BoujeeEnjinia1701/thermabrick/cad/drawings/TBK-DWG-001.pdf

CONCEPT, NOT FOR FABRICATION | ThermaBrick · github.com/BoujeeEnjinia1701/thermabrick

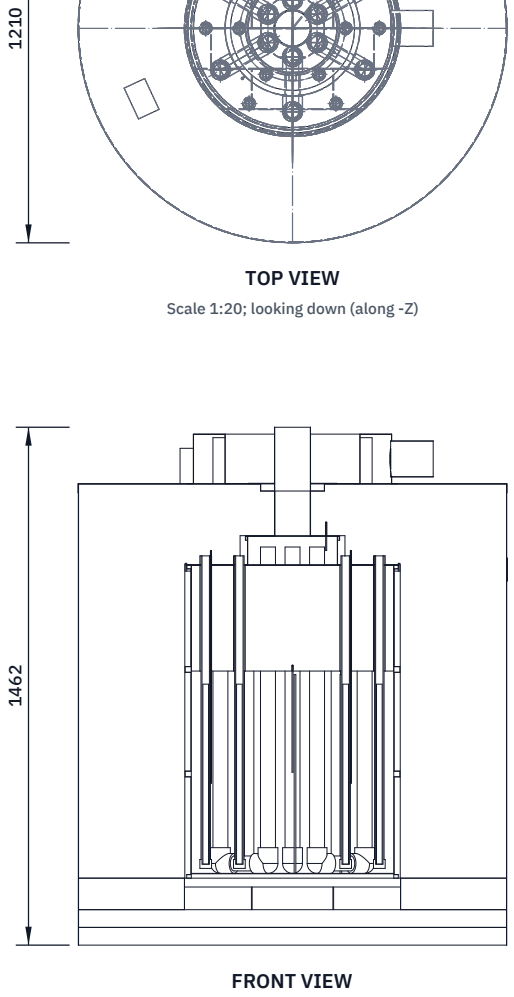
[picture p46: figure]
FRONT VIEW; TOP VIEW; Scale 1:20; looking down (along -Z)

Scale 1:20; looking at the front (along +Y)

RIGHT VIEW
Scale 1:20; looking at the right side (along -X)

1212

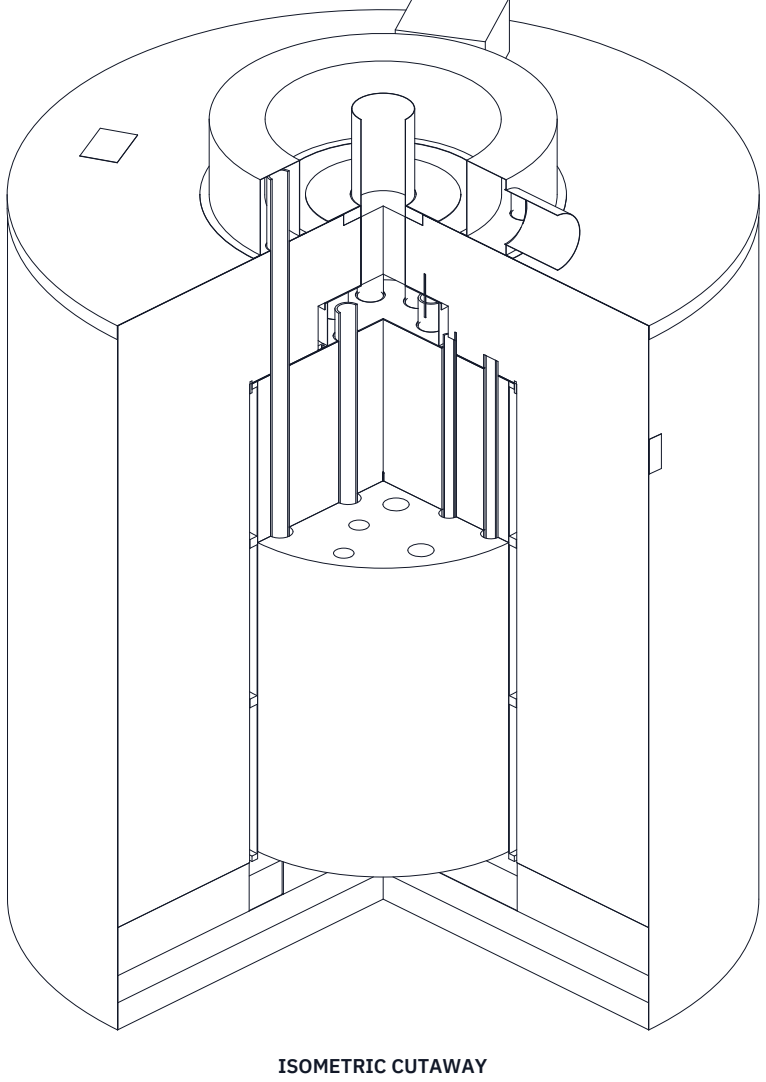
[picture p47: figure]
ISOMETRIC CUTAWAY

Quarter removed, not to scale; seen from the front right and above, about 30 deg elevation

KEY DATA AND NOTES
STORAGE | 210 kg dry silica sand, 18.3 kWh(th) between 150 and 450 °C mean
CHARGE | 12 cartridge heaters, 250 W each, 3.0 kW at 240 V; sand and well wall 550 °C max
DISCHARGE | Six 1-1/4 in U-tubes, 1.0 kW rated, 1.5 kW boost; supply air 50 °C via mixing tee
ENVELOPE | 1,209 mm dia x 1,462 mm high; about 415 kg; slab floor only
SECTION A-A | Front view is cut on the XZ plane through four heater wells; sand omitted for clarity
SAND LEVEL | 571 mm above drum floor; headspace filled with 298 mm AES blanket and stone wool
LABELS | HOT SURFACES INSIDE on the jacket, HOT OUTLET on the cap, DANGER 240 V on the junction box (96 x 64 and 90 x 44 mm)
REFERENCE | TBK-PRC-001 design precis, TBK-CAL-001 sizing, TBK-BLD-001 build plan, bom/bom.csv
REV | DESCRIPTION | DATE | BY
P1 | First issue: general arrangement of the v0.2 design | 2026-09-24 | AC
P2 | Made constructable: base, fittings, plenum, cap, box (TBK-DDR-003) | 2026-09-30 | AC
P3 | Warning labels added: jacket, cap, junction box (BOM line 47, TBK-DEC-001) | 2026-10-02 | AC
THERMABRICK | github.com/BoujeeEnjinia1701/thermabrick

# General arrangement

DRAWING NO.
TBK-DWG-001

REV
P3

SHEET
1 of 1

SIZE

## ANSI B

SCALE
1:20

UNITS
mm
PROJECTION | DATE
2026-10-02

DRAWN

### Amish Chadha

MATERIAL / NOTES
Carbon steel drum and pipe; AES blanket and stone wool; galvanized jacket. See bom/bom.csv
Licensed CERN-OHL-S-2.0 · Design Molecule Lab · designmolecule.com | Generated from cad/src; do not edit by hand
