BoujeeEnjinia1701/thermabrick/cad/drawings/TBK-DWG-101.pdf

BUILD PLAN SKETCH, PLAN NOT YET BUILT ThermaBrick · github.com/BoujeeEnjinia1701/thermabrick

FRONT VIEW
Scale 1:20; looking at the front (along +Y)

TOP VIEW
Scale 1:20; looking down (along -Z)

RIGHT VIEW
Scale 1:20; looking at the right side (along -X)

1208

1208 189

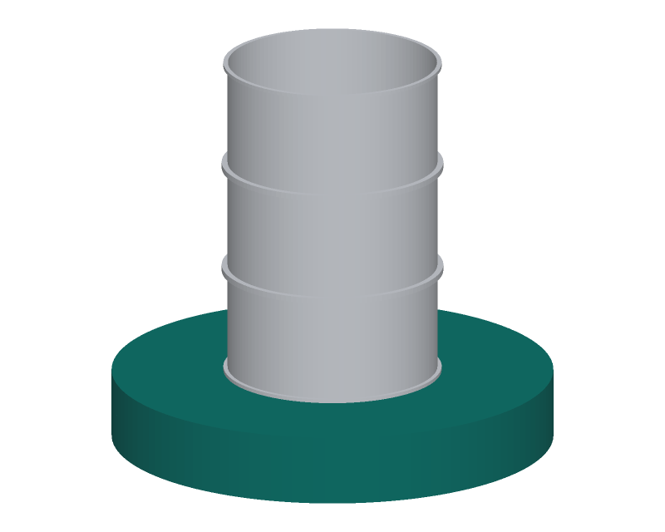
[picture p48: figure]

WHERE IT GOES
This part in colour, its neighbours in grey

HOW TO MAKE IT AND HOW IT FITS
Four layers, 189 mm in all, 1,208 mm across (the inside of the jacket).
Boards: two layers of 50 mm stone wool board, each from two 610 x 1,219 mm boards butted into a 1,219 mm square and cut to a 1,208 mm disc.
Turn the top layer 90 degrees so the joints cross.
Firebrick: one course laid flat (64 mm), 610 mm disc in the middle,
bricks in staggered rows, cut with a saw to the circle (layout picture).
AES board: one 25 mm board cut to a 610 mm disc, laid on the bricks. Ring: 89 mm stone wool batt cut into segments to fill from the 610 mm disc out to 1,208 mm, level with the top of the AES board.
Fit: the drum's bottom rim (597 mm) stands on the AES disc, 6 mm in from its edge, over the firebrick, which carries the load.
Check: the top is flat within 3 mm across a straight edge.
REV | DESCRIPTION | DATE | BY
P1 | Making sketch for the prototype build plan | 2026-09-30 | AC
THERMABRICK | github.com/BoujeeEnjinia1701/thermabrick

## ThermaBrick base: making sketch

DRAWING NO.
TBK-DWG-101

REV
P1

SHEET
1 of 1

SIZE

## ANSI B

SCALE
1:20

UNITS
mm
PROJECTION | DATE
2026-09-30

DRAWN
Amish Chadha

MATERIAL / NOTES
Stone wool board 50 mm; K-23 firebrick; AES board 25 mm; stone wool batt 89 mm
Licensed CERN-OHL-S-2.0 · Design Molecule Lab · designmolecule.com | Generated from cad/src; do not edit by hand
