BoujeeEnjinia1701/thermabrick/cad/drawings/TBK-DWG-102.pdf

BUILD PLAN SKETCH, PLAN NOT YET BUILT ThermaBrick · github.com/BoujeeEnjinia1701/thermabrick

FRONT VIEW
Scale 1:10; looking at the front (along +Y)

TOP VIEW
Scale 1:10; looking down (along -Z)

RIGHT VIEW
Scale 1:10; looking at the right side (along -X)

606

606 22

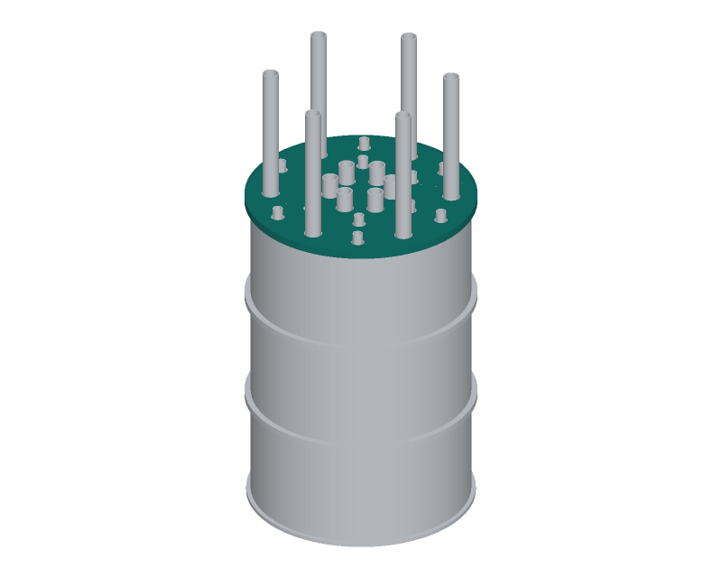
[picture p49: figure]

WHERE IT GOES
This part in colour, its neighbours in grey

HOW TO MAKE IT AND HOW IT FITS
Drill the lid with the template (TBK-DWG-103) clamped on it as a guide. Twelve 36 mm holes for the heater wells: six on a 150 mm radius at
0, 60, 120 ... degrees and six on a 245 mm radius at the same angles. Twelve 48 mm holes for the U-tube legs: six on 80 mm and six on 235 mm radius at 30, 90, 150 ... degrees (between the wells).
Four 6 mm holes for the sand thermocouples (lid layout picture).
Cut with bi-metal hole saws at low speed with cutting oil; deburr.
Mark a line at 0 degrees on the lid and the drum rim to line them up. Fit: the lid drops over all 24 pipe ends, the well holes leaving a
4.6 mm gap (a T1 to T3 sheath fits beside its well) and the leg holes 2.9 mm. An AES rope collar is laid round every pipe on the lid. Check: lay the template on the lid; every hole lines up.
REV | DESCRIPTION | DATE | BY
P1 | Making sketch for the prototype build plan | 2026-09-30 | AC
THERMABRICK | github.com/BoujeeEnjinia1701/thermabrick

## ThermaBrick drum lid: drilling sketch

DRAWING NO.
TBK-DWG-102

REV
P1

SHEET
1 of 1

SIZE

## ANSI B

SCALE
1:10

UNITS
mm
PROJECTION | DATE
2026-09-30

DRAWN
Amish Chadha

MATERIAL / NOTES
The drum's own 16 ga steel lid and bolted closing ring
Licensed CERN-OHL-S-2.0 · Design Molecule Lab · designmolecule.com | Generated from cad/src; do not edit by hand
