BoujeeEnjinia1701/thermabrick/cad/drawings/TBK-DWG-103.pdf

BUILD PLAN SKETCH, PLAN NOT YET BUILT ThermaBrick · github.com/BoujeeEnjinia1701/thermabrick

FRONT VIEW
Scale 1:10; looking at the front (along +Y)

TOP VIEW
Scale 1:10; looking down (along -Z)

RIGHT VIEW
Scale 1:10; looking at the right side (along -X)

597

597 18

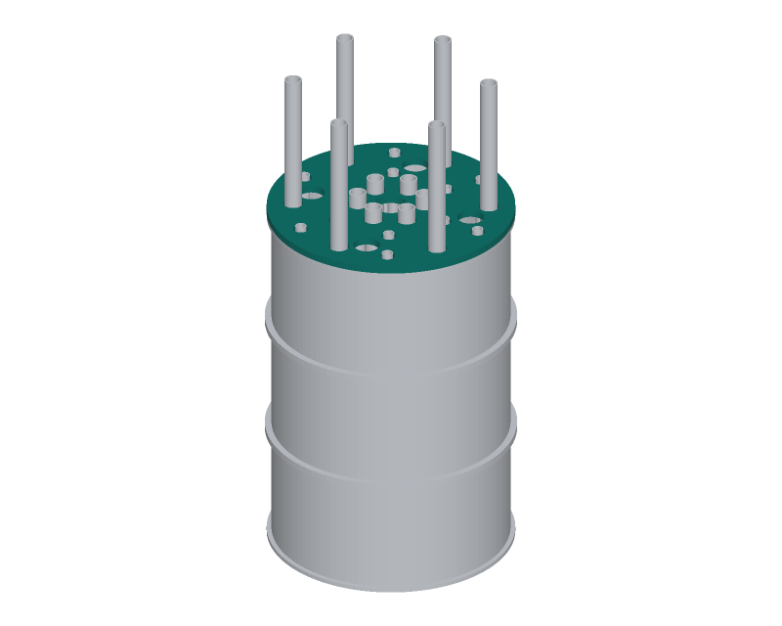
[picture p50: figure]

WHERE IT GOES
This part in colour, its neighbours in grey

HOW TO MAKE IT AND HOW IT FITS
A temporary jig. Cut a 597 mm disc from 18 mm plywood: it sits on the drum's top rim, where the lid will go.
Drill the same holes as the lid (36 mm wells, 48 mm legs, 6 mm sheaths) from the lid layout picture, with the 0 degree line marked.
Pour holes: one 80 mm hole in the centre and four 64 mm holes on a 200 mm radius at 15, 105, 195 and 285 degrees.
Drill the template first and use it to drill the lid, so both match.
Fit: the template drops over the pipe ends and holds every well, U-tube leg and sheath upright while sand is poured through the pour holes. Lift it off before the headspace insulation goes in.
Check: it lies flat on the rim with all 24 pipes through it.
REV | DESCRIPTION | DATE | BY
P1 | Making sketch for the prototype build plan | 2026-09-30 | AC
THERMABRICK | github.com/BoujeeEnjinia1701/thermabrick

## ThermaBrick setting template: making sketch

DRAWING NO.
TBK-DWG-103

REV
P1

SHEET
1 of 1

SIZE

## ANSI B

SCALE
1:10

UNITS
mm
PROJECTION | DATE
2026-09-30

DRAWN
Amish Chadha

MATERIAL / NOTES
Exterior plywood 18 mm
Licensed CERN-OHL-S-2.0 · Design Molecule Lab · designmolecule.com | Generated from cad/src; do not edit by hand
