BoujeeEnjinia1701/thermabrick/cad/drawings/TBK-DWG-104.pdf

BUILD PLAN SKETCH, PLAN NOT YET BUILT ThermaBrick · github.com/BoujeeEnjinia1701/thermabrick

FRONT VIEW
Scale 1:10; looking at the front (along +Y)

TOP VIEW
Scale 1:10; looking down (along -Z)

RIGHT VIEW
Scale 1:10; looking at the right side (along -X)

33

33 882

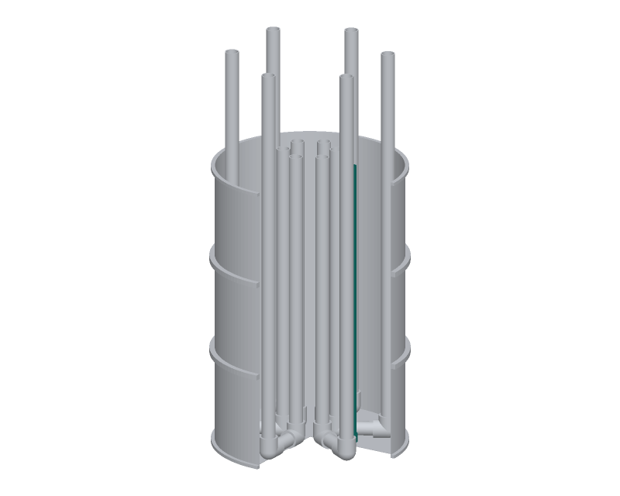
[picture p51: figure]

WHERE IT GOES
This part in colour, its neighbours in grey

HOW TO MAKE IT AND HOW IT FITS
Cut twelve lengths of 876 mm from four 10 ft pipes (three per pipe). Thread one end 3/4 in NPT (rented pipe threader); ream and deburr. Clean off cutting oil with degreaser: oil smokes on first heat.
Coat the thread with nickel anti-seize (no PTFE tape or paste) and screw on the cap hand tight plus one and a half turns.
The open top end is square cut and deburred so a heater slides in. Fit: the cap stands on a levelled 14 mm first lift of sand; the template and then the lid hold the top, which ends 25 mm above the lid.
Each 508 mm heater rests on the cap inside, its heated part 26 to 483 mm above the drum floor; its leads rise out of the open top. Check: length 876 mm plus cap, within 3 mm; a 16 mm rod slides to the bottom freely.
REV | DESCRIPTION | DATE | BY
P1 | Making sketch for the prototype build plan | 2026-09-30 | AC
THERMABRICK | github.com/BoujeeEnjinia1701/thermabrick

## ThermaBrick heater well (make 12): making sketch

DRAWING NO.
TBK-DWG-104

REV
P1

SHEET
1 of 1

SIZE

## ANSI B

SCALE
1:10

UNITS
mm
PROJECTION | DATE
2026-09-30

DRAWN
Amish Chadha

MATERIAL / NOTES
Black steel pipe 3/4 in Sch 40 (26.7 mm), malleable iron cap 3/4 in NPT
Licensed CERN-OHL-S-2.0 · Design Molecule Lab · designmolecule.com | Generated from cad/src; do not edit by hand
