BoujeeEnjinia1701/thermabrick/cad/drawings/TBK-DWG-105.pdf

BUILD PLAN SKETCH, PLAN NOT YET BUILT ThermaBrick · github.com/BoujeeEnjinia1701/thermabrick

FRONT VIEW
Scale 1:10; looking at the front (along +Y)

TOP VIEW
Scale 1:10; looking down (along -Z)

RIGHT VIEW
Scale 1:10; looking at the right side (along -X)

211

56 1230

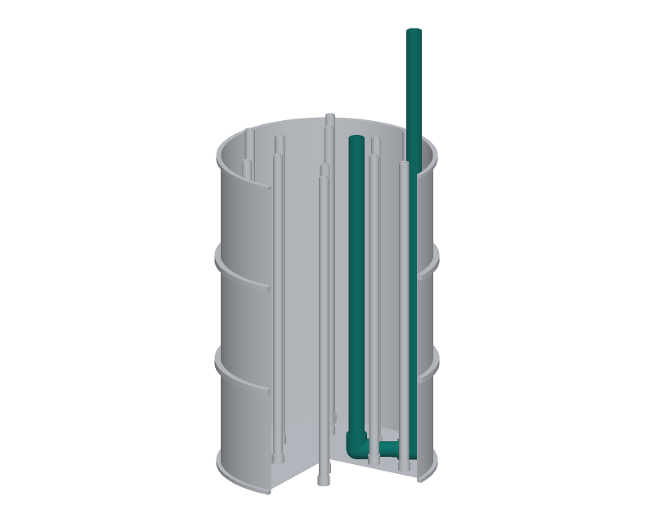
[picture p52: figure]

WHERE IT GOES
This part in colour, its neighbours in grey

HOW TO MAKE IT AND HOW IT FITS
Cut six inlet legs 1175 mm long (two per 10 ft pipe) and six outlet legs 866 mm (three per pipe). Thread one end of each. Degrease, coat every thread with nickel anti-seize, then join: outlet leg, elbow, 4 in nipple, elbow, inlet leg, wrench tight. Turn the second elbow so both legs stand parallel, in one plane. Leg centres 155 mm apart (the fittings make 155.6 mm).
The elbows rest on the drum floor; the run is 28 mm above it.
Fit: the short leg (outlet) stands on the 80 mm circle and ends inside the collector; the long leg (inlet) on the 235 mm circle, ending inside the inlet plenum, 130 mm above the jacket cap.
Check: legs parallel within 3 mm over their length; blow through
it to clear swarf.
REV | DESCRIPTION | DATE | BY
P1 | Making sketch for the prototype build plan | 2026-09-30 | AC
THERMABRICK | github.com/BoujeeEnjinia1701/thermabrick

## ThermaBrick U-tube (make 6): making sketch

DRAWING NO.
TBK-DWG-105

REV
P1

SHEET
1 of 1

SIZE

## ANSI B

SCALE
1:10

UNITS
mm
PROJECTION | DATE
2026-09-30

DRAWN
Amish Chadha

MATERIAL / NOTES
Black steel pipe 1-1/4 in Sch 40; two 90 degree elbows; 1-1/4 x 4 in nipple
Licensed CERN-OHL-S-2.0 · Design Molecule Lab · designmolecule.com | Generated from cad/src; do not edit by hand
