BoujeeEnjinia1701/thermabrick/cad/drawings/TBK-DWG-106.pdf

BUILD PLAN SKETCH, PLAN NOT YET BUILT ThermaBrick · github.com/BoujeeEnjinia1701/thermabrick

FRONT VIEW
Scale 1:10; looking at the front (along +Y)

TOP VIEW
Scale 1:10; looking down (along -Z)

RIGHT VIEW
Scale 1:10; looking at the right side (along -X)

266

293 388

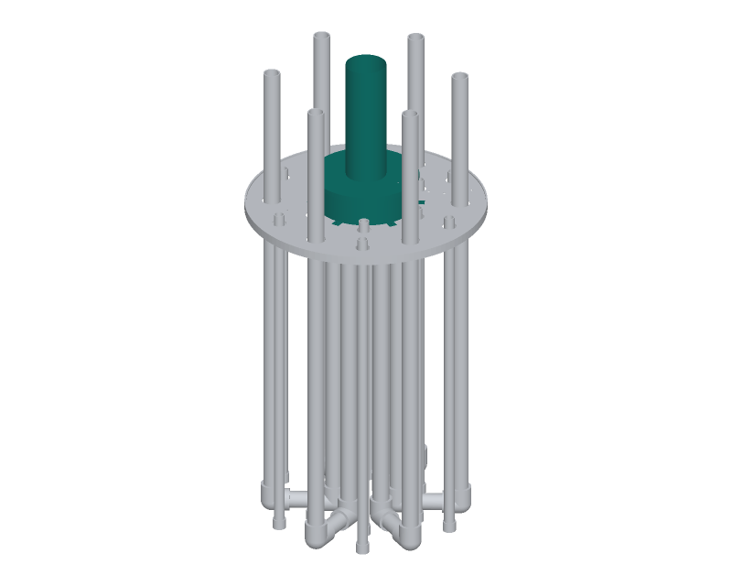
[picture p53: figure]

WHERE IT GOES
This part in colour, its neighbours in grey

HOW TO MAKE IT AND HOW IT FITS
Ring: cut an 80 mm band from 10 in (254 mm) black stovepipe. Tabs: at the foot, at 30, 90, 150 ... degrees, cut six slits 20 mm deep and 20 mm apart and fold the tabs out flat. Drill each for a 4.8 mm steel rivet, 10 mm from the ring.
Top: cut a 266 mm disc from 18 ga uncoated steel, fold a 12 mm edge down over the ring and rivet it in six places.
Cut a 4 in hole in the middle and rivet in the 4 in crimped start collar; fit the 4 in pipe to 160 mm above the jacket cap.
Drill a 4 mm hole 95 mm from the centre for thermocouple T8.
Fit: tabs riveted to the lid between the inner wells; AES rope pressed round the foot of the ring. The six short legs end inside it.
No zinc: use uncoated steel and steel rivets only.
REV | DESCRIPTION | DATE | BY
P1 | Making sketch for the prototype build plan | 2026-09-30 | AC
THERMABRICK | github.com/BoujeeEnjinia1701/thermabrick

## ThermaBrick collector and outlet: making sketch

DRAWING NO.
TBK-DWG-106

REV
P1

SHEET
1 of 1

SIZE

## ANSI B

SCALE
1:10

UNITS
mm
PROJECTION | DATE
2026-09-30

DRAWN
Amish Chadha

MATERIAL / NOTES
10 in black stovepipe 24 ga; 18 ga steel sheet; 4 in start collar and pipe
Licensed CERN-OHL-S-2.0 · Design Molecule Lab · designmolecule.com | Generated from cad/src; do not edit by hand
