BoujeeEnjinia1701/thermabrick/cad/drawings/TBK-DWG-107.pdf

BUILD PLAN SKETCH, PLAN NOT YET BUILT ThermaBrick · github.com/BoujeeEnjinia1701/thermabrick

FRONT VIEW
Scale 1:20; looking at the front (along +Y)

TOP VIEW
Scale 1:20; looking down (along -Z)

RIGHT VIEW
Scale 1:20; looking at the right side (along -X)

1209

1209 1302

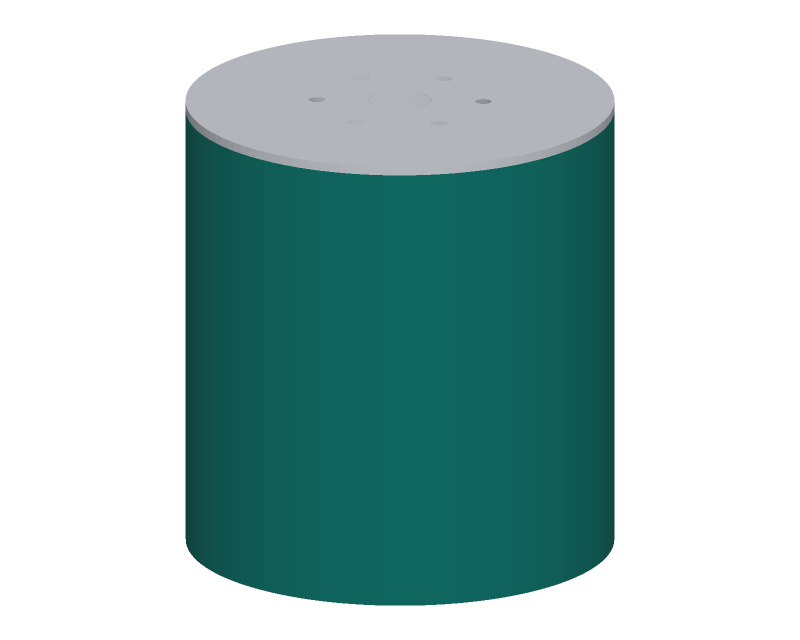
[picture p54: figure]

WHERE IT GOES
This part in colour, its neighbours in grey

HOW TO MAKE IT AND HOW IT FITS
Three rows of 610 mm flashing, each 3,850 mm long (3,800 mm round plus a 50 mm lap), wrapped round the side insulation.
Bottom row on the floor; the second laps 25 mm outside it; the top row is cut to width so the side ends 1,302 mm above the floor.
Pull each row tight with ratchet straps over the insulation, then rivet the vertical lap every 100 mm with 4.8 mm aluminium rivets. Rivet the row laps every 150 mm. Stagger the vertical laps.
Inside diameter 1,208 mm: the insulation is 317 mm thick all round. Fit: the cap's 25 mm skirt sits outside the top row and is held by sheet metal screws (not rivets) so the cap can come off.
The jacket runs at about 26 degrees C, so galvanized steel is fine. Check: round within 10 mm on two diameters; no gaps at the laps.
REV | DESCRIPTION | DATE | BY
P1 | Making sketch for the prototype build plan | 2026-09-30 | AC
THERMABRICK | github.com/BoujeeEnjinia1701/thermabrick

## ThermaBrick jacket side: making sketch

DRAWING NO.
TBK-DWG-107

REV
P1

SHEET
1 of 1

SIZE

## ANSI B

SCALE
1:20

UNITS
mm
PROJECTION | DATE
2026-09-30

DRAWN
Amish Chadha

MATERIAL / NOTES
Galvanized steel flashing 0.6 mm, 610 mm wide coil
Licensed CERN-OHL-S-2.0 · Design Molecule Lab · designmolecule.com | Generated from cad/src; do not edit by hand
