BoujeeEnjinia1701/thermabrick/cad/drawings/TBK-DWG-108.pdf

BUILD PLAN SKETCH, PLAN NOT YET BUILT ThermaBrick · github.com/BoujeeEnjinia1701/thermabrick

FRONT VIEW
Scale 1:20; looking at the front (along +Y)

TOP VIEW
Scale 1:20; looking down (along -Z)

RIGHT VIEW
Scale 1:20; looking at the right side (along -X)

1210

1210 26

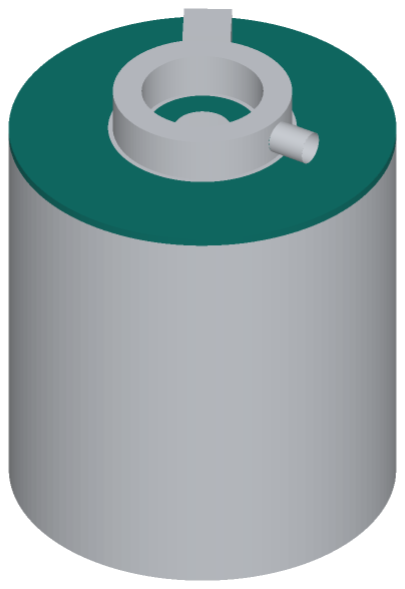
[picture p55: figure]

WHERE IT GOES
This part in colour, its neighbours in grey

HOW TO MAKE IT AND HOW IT FITS
Three strips of 610 mm flashing, 1,260 mm long, lapped 25 mm and riveted into one sheet; cut a 1,260 mm disc.
Snip the edge every 50 mm, 25 mm deep, and turn it down 90 degrees to make the skirt (1,210 mm inside).
Holes (cap layout picture): 180 mm in the centre for the outlet; six
46 mm on a 235 mm radius at 30, 90 ... degrees for the inlet legs;
40 mm at 120 degrees, 430 mm out, under the junction box; 25 mm at 95 degrees, 330 mm out, for the thermocouple exit.
Fit grommets in the 40 and 25 mm holes; foil tape round the legs. Fit: it lowers over the six inlet legs and the outlet and rests on the
top insulation; eight screws through the skirt into the side. Check: every hole lines up with its pipe before it is pressed down.
REV | DESCRIPTION | DATE | BY
P1 | Making sketch for the prototype build plan | 2026-09-30 | AC
THERMABRICK | github.com/BoujeeEnjinia1701/thermabrick

## ThermaBrick jacket cap: making sketch

DRAWING NO.
TBK-DWG-108

REV
P1

SHEET
1 of 1

SIZE

## ANSI B

SCALE
1:20

UNITS
mm
PROJECTION | DATE
2026-09-30

DRAWN
Amish Chadha

MATERIAL / NOTES
Galvanized steel flashing 0.6 mm, 610 mm wide coil
Licensed CERN-OHL-S-2.0 · Design Molecule Lab · designmolecule.com | Generated from cad/src; do not edit by hand
