BoujeeEnjinia1701/thermabrick/cad/drawings/TBK-DWG-109.pdf

BUILD PLAN SKETCH, PLAN NOT YET BUILT ThermaBrick · github.com/BoujeeEnjinia1701/thermabrick

FRONT VIEW
Scale 1:5; looking at the front (along +Y)

TOP VIEW
Scale 1:5; looking down (along -Z)

RIGHT VIEW
Scale 1:5; looking at the right side (along -X)

250

250 1

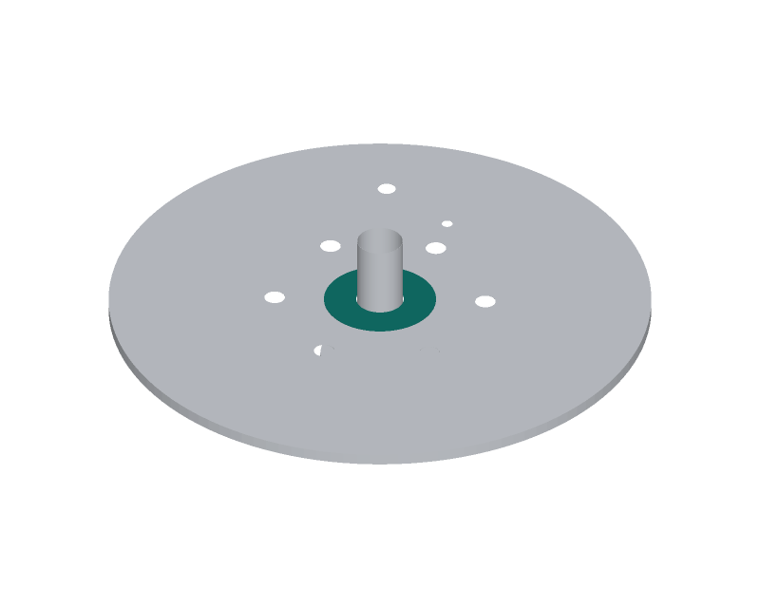
[picture p56: figure]

WHERE IT GOES
This part in colour, its neighbours in grey

HOW TO MAKE IT AND HOW IT FITS
Cut a 250 mm disc from 18 ga uncoated steel with snips; file the edge. Cut a 106 mm hole in the middle (2.3 mm clear of the 4 in pipe).
Drill four 3.5 mm holes on a 230 mm circle for sheet metal screws.
Fit: the 180 mm hole in the galvanized cap leaves a 39 mm gap round the hot outlet. Pack the gap with AES blanket (20 mm deep), then lay the ring over it and screw it to the cap at its outer edge.
The ring, not the cap, faces the hot pipe, so no zinc sits within
39 mm of it (requirement R13: no zinc above 200 degrees C). Check: the ring does not touch the pipe at any point.
REV | DESCRIPTION | DATE | BY
P1 | Making sketch for the prototype build plan | 2026-09-30 | AC
THERMABRICK | github.com/BoujeeEnjinia1701/thermabrick

## ThermaBrick outlet trim ring: making sketch

DRAWING NO.
TBK-DWG-109

REV
P1

SHEET
1 of 1

SIZE

## ANSI B

SCALE
1:5

UNITS
mm
PROJECTION | DATE
2026-09-30

DRAWN
Amish Chadha

MATERIAL / NOTES
Uncoated (black) steel sheet 18 ga (1.2 mm)
Licensed CERN-OHL-S-2.0 · Design Molecule Lab · designmolecule.com | Generated from cad/src; do not edit by hand
