BoujeeEnjinia1701/thermabrick/cad/drawings/TBK-DWG-110.pdf

BUILD PLAN SKETCH, PLAN NOT YET BUILT ThermaBrick · github.com/BoujeeEnjinia1701/thermabrick

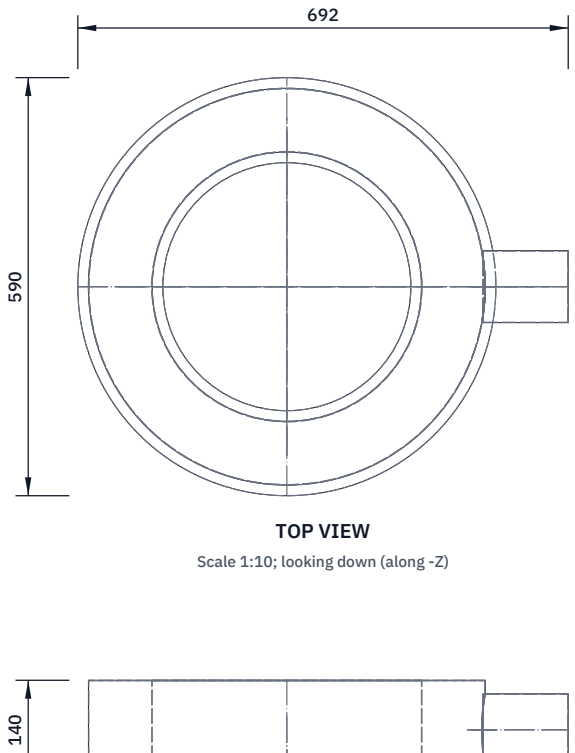
[picture p57: figure]
TOP VIEW; Scale 1:10; looking down (along -Z)

FRONT VIEW
Scale 1:10; looking at the front (along +Y)

RIGHT VIEW
Scale 1:10; looking at the right side (along -X)

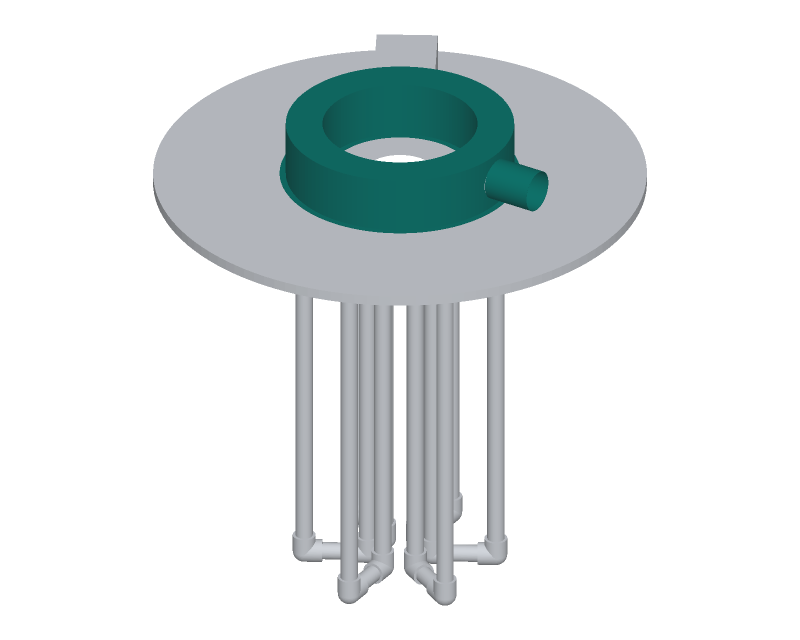
[picture p58: figure]

WHERE IT GOES
This part in colour, its neighbours in grey

HOW TO MAKE IT AND HOW IT FITS
An annular box 140 mm high, 380 mm inside and 560 mm outside. Walls: strips 170 mm wide (140 high plus a 15 mm flange and a 15 mm tab edge), 1,780 mm long for the outer wall and 1,220 mm for the inner, rolled round and riveted at a 25 mm lap.
Top: an annulus 560 mm outside, 380 mm inside, from flashing.
Snip the tab edges every 40 mm, fold them over the top and rivet.
Snip the foot edges and fold them out (outer wall) and in (inner wall) as 15 mm flanges.
Collar: cut a 4 in hole in the outer wall at 0 degrees, centred 70 mm up, and rivet in the crimped start collar (19 mm of wall each side). Fit: flanges riveted to the cap; the six inlet legs end 10 mm below the top inside it. Seal the flanges with foil tape.
REV | DESCRIPTION | DATE | BY
P1 | Making sketch for the prototype build plan | 2026-09-30 | AC
THERMABRICK | github.com/BoujeeEnjinia1701/thermabrick

## ThermaBrick inlet plenum: making sketch

DRAWING NO.
TBK-DWG-110

REV
P1

SHEET
1 of 1

SIZE

## ANSI B

SCALE
1:10

UNITS
mm
PROJECTION | DATE
2026-09-30

DRAWN
Amish Chadha

MATERIAL / NOTES
Galvanized steel flashing 0.6 mm; 4 in crimped start collar
Licensed CERN-OHL-S-2.0 · Design Molecule Lab · designmolecule.com | Generated from cad/src; do not edit by hand
