BoujeeEnjinia1701/thermabrick/cad/drawings/TBK-DWG-005.pdf

## CONCEPT, NOT FOR FABRICATION

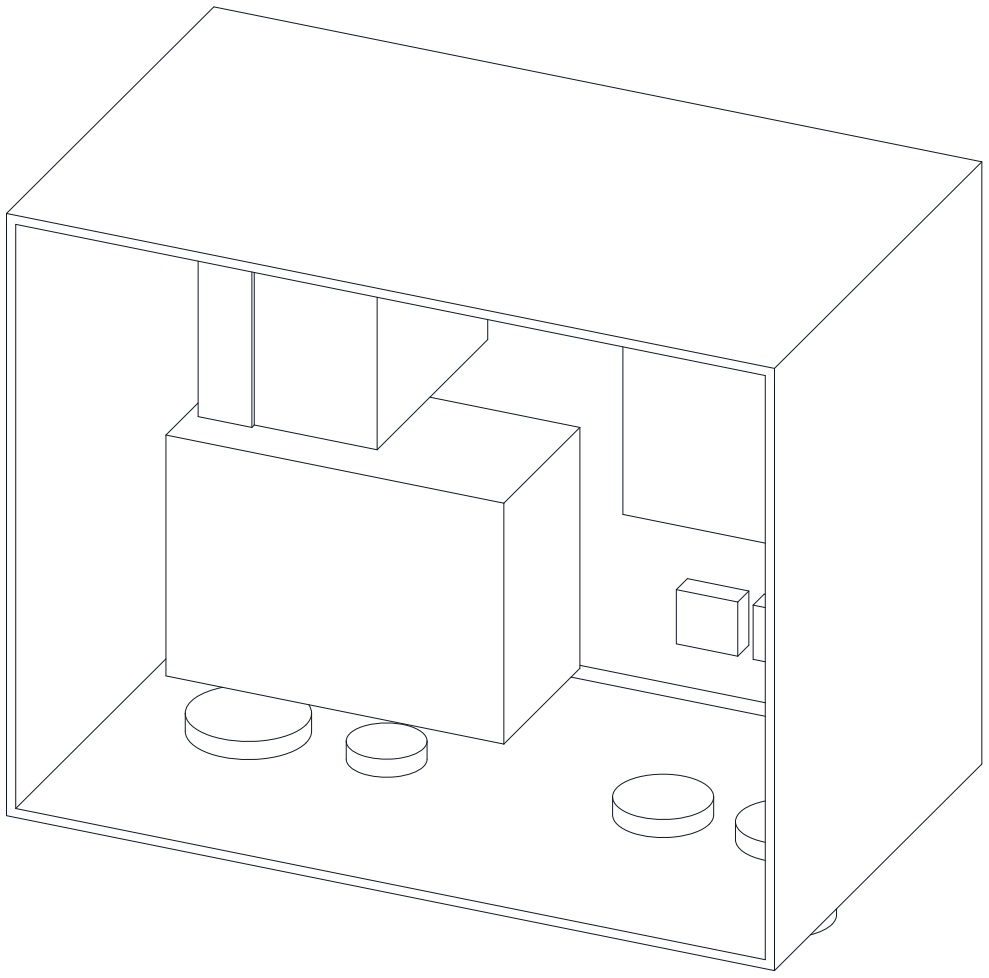
[picture p59: figure]

### FRONT VIEW

Scale 1:5

### TOP VIEW

Scale 1:5

### RIGHT VIEW

Scale 1:5

### ISOMETRIC, LID REMOVED

Lid parts hidden, not to scale

KEY DATA AND NOTES

ENCLOSURE | 250 x 200 x 150 mm polycarbonate, UL 94 V-0 or 5VA, IP65; steel mounting plate bonded to PE
LID CUTOUTS | REX-C100 45 x 45 mm at x 60, z 55; STOP and START 22.5 mm dia at x -25 and 10, z 55
GLANDS | Bottom face at y 75: M25 x -80 (thermocouples), M16 x -35 (blower), M20 x 55 (supply), M20 x 95 (heaters)
PLATE | DIN rail at z 145: HDR-15-12 12 V supply, JQX-30F relay socket. SSR on heat sink top right; controller bottom left
CLEARANCE | Fit check: every part clears by 3 mm; REX-C100 body ends 36 mm from the plate
DATUM | x from the enclosure centerline, z up from the bottom face, y into the box from the lid
REFERENCE | TBK-DWG-003 schematic, TBK-PRC-002, bom/bom-test-article.csv
REV | DESCRIPTION | DATE | BY
P1 | First issue: controller enclosure, 250 x 200 x 150 mm | 2026-09-24 | AC

THERMABRICK

# Controller enclosure layout

DRAWING NO.

## TBK-DWG-005

REV
P1

SHEET
1 of 1

SIZE

## ANSI B

SCALE
1:5

UNITS
mm
PROJECTION | DATE
2026-09-24

DRAWN

## Amish Chadha

MATERIAL / NOTES
Polycarbonate enclosure, steel mounting plate. Part envelopes from supplier data
Licensed CERN-OHL-S-2.0 · Open Hardware Portfolio · amishchadha.com | Generated from cad/src; do not edit by hand
