BoujeeEnjinia1701/thermabrick/archive/out-of-phase-trl4/README.md

# Out-of-phase work (TRL 4 material), archived

Archived on 2026-09-25 at Amish's instruction. The portfolio is capped at TRL 3 (`.kit/PHASE.yaml`), and TRL 4 is on hold for every repo.

An earlier session on 2026-09-24 went past the TRL 3 cap and produced the material below for a reduced-scale test article. It was moved here unchanged, with its git history intact. Nothing was deleted. It is **not current work**: do not extend it, build from it or cite it as evidence until Amish lifts the cap.

| Item | Path in this folder |
| --- | --- |
| Test article precis TBK-PRC-002 | `docs/06-test-article.md` |
| Test article sizing TBK-CAL-002 and script | `docs/04-calcs/` |
| Test plan TBK-TST-001, report template TBK-TST-002, analysis and fill scripts | `docs/05-tests/` |
| Build procedure and cut list | `docs/07-build/` |
| Test article, schematic, board and enclosure drawings TBK-DWG-002 to TBK-DWG-005 | `cad/drawings/` |
| Test article and enclosure models, STEP and STL; full `sheets.py` that builds DWG-002 and DWG-005 | `cad/src/`, `cad/step/`, `cad/stl/` |
| KiCad schematic, optional controller board and Gerbers | `electronics/` |
| ESP32 firmware and logging host | `firmware/` |
| Test article and controller board BOMs, purchasing checklist | `bom/` |
| Build log template and entry helper | `build-log/` |
| Rendered PDFs of the archived documents | `docs/pdf/` |

The budget decision Amish made for this test article ($635.70, 2026-09-24) stands but is on hold with the rest of TRL 4. The rise to $727.70 remains "Proposed, awaiting Amish".

Paths inside these files still refer to their original locations. The scripts will not run from here without moving the files back.
