BoujeeEnjinia1701/thermabrick/cad/drawings/TBK-DWG-001.png

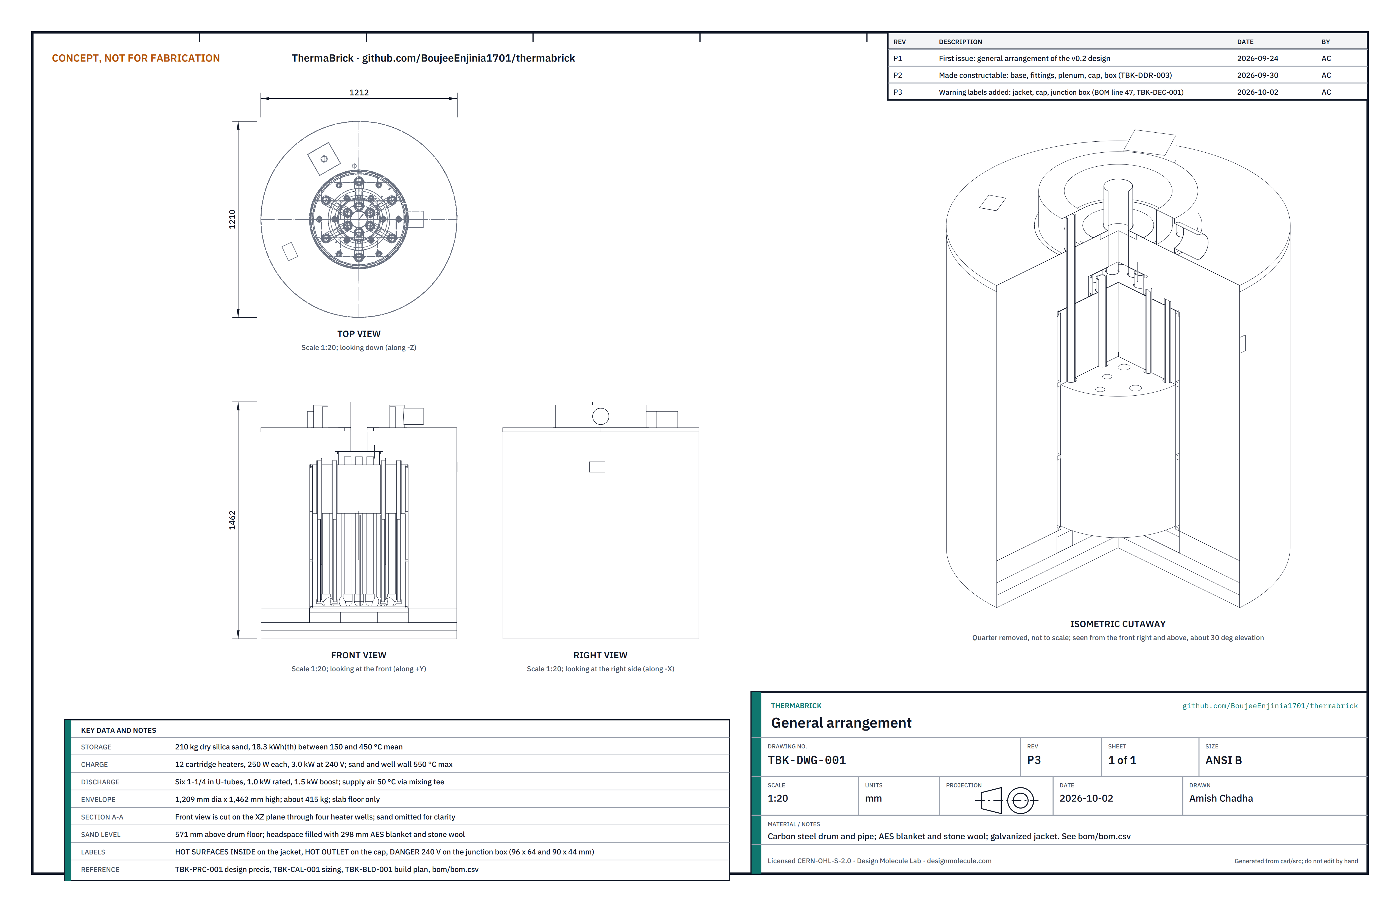
cad/drawings/TBK-DWG-001.png
