BoujeeEnjinia1701/thermabrick/cad/drawings/TBK-DWG-002.png

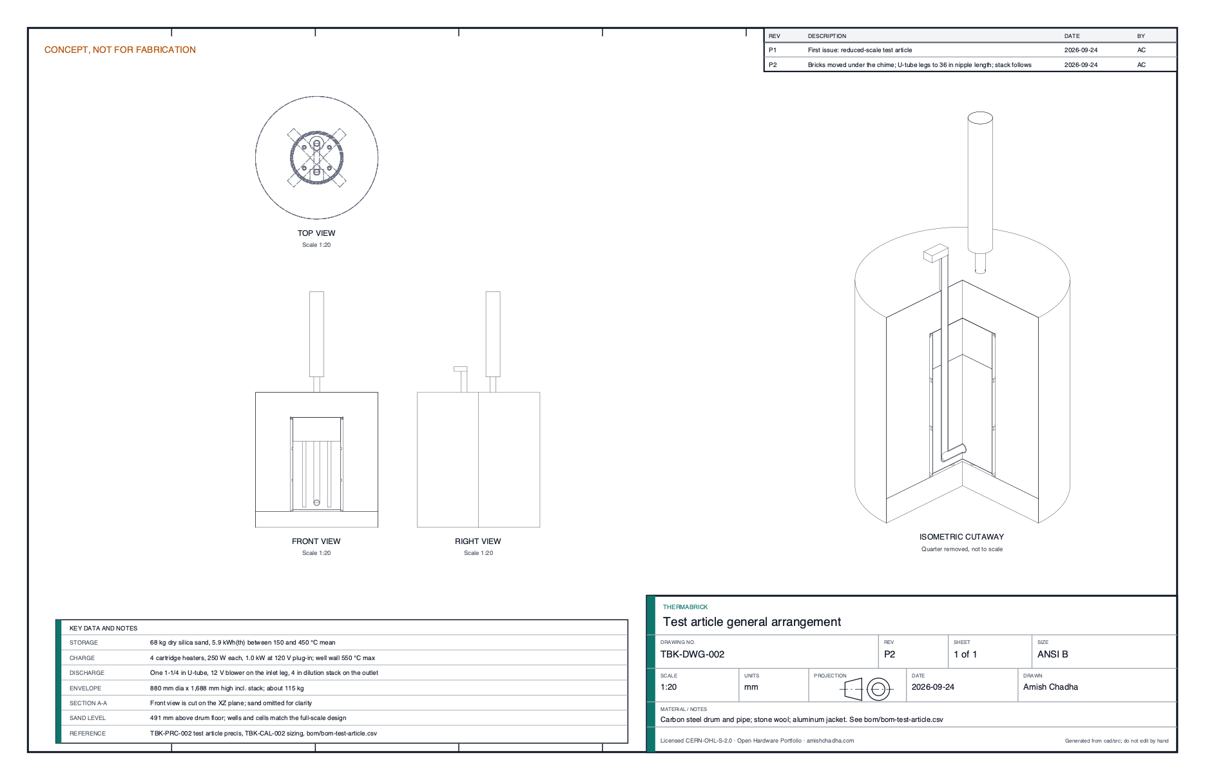
cad/drawings/TBK-DWG-002.png
