BoujeeEnjinia1701/thermabrick/cad/drawings/TBK-DWG-003.png

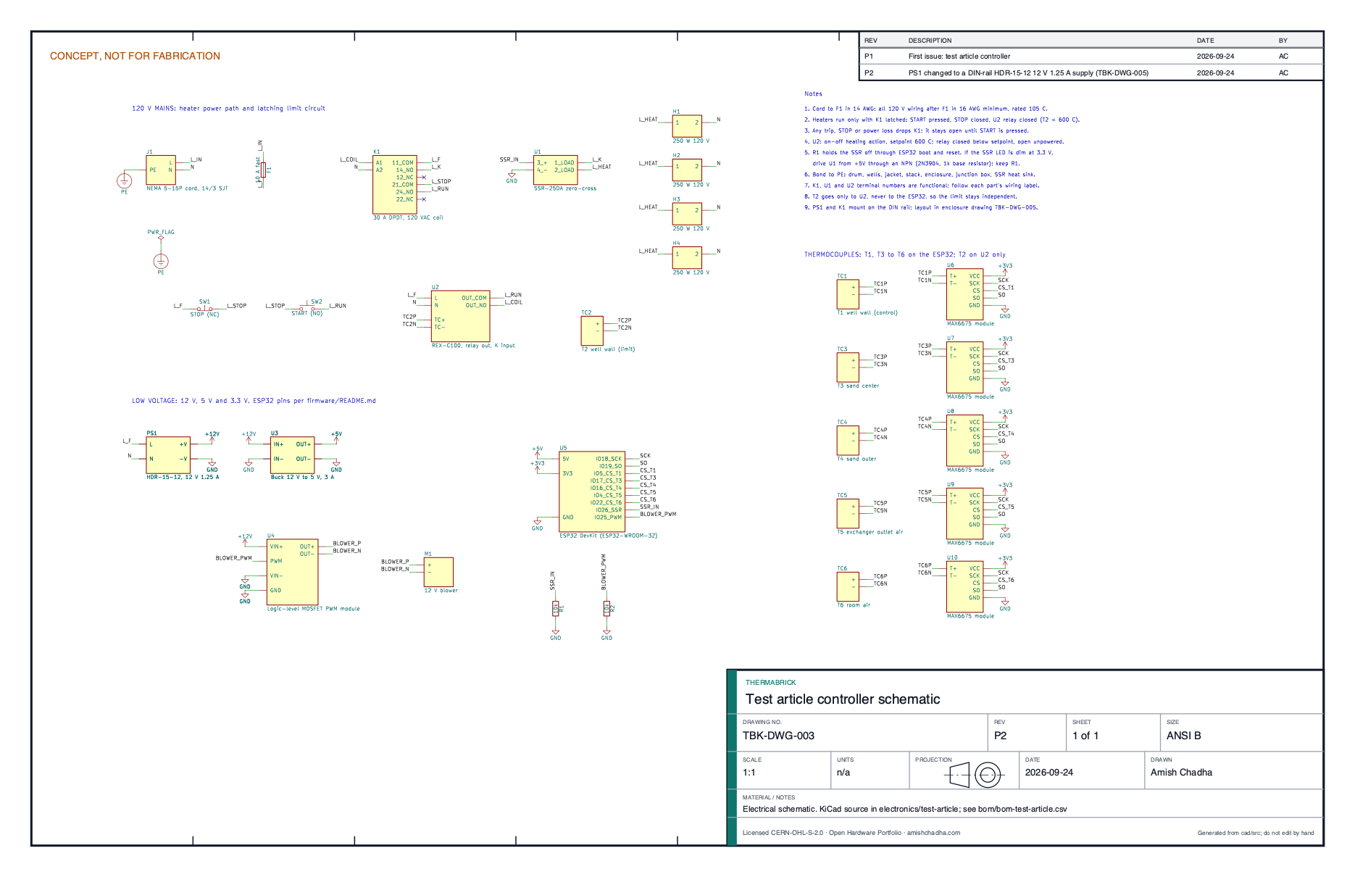
cad/drawings/TBK-DWG-003.png
