BoujeeEnjinia1701/thermabrick/cad/drawings/TBK-DWG-004.png

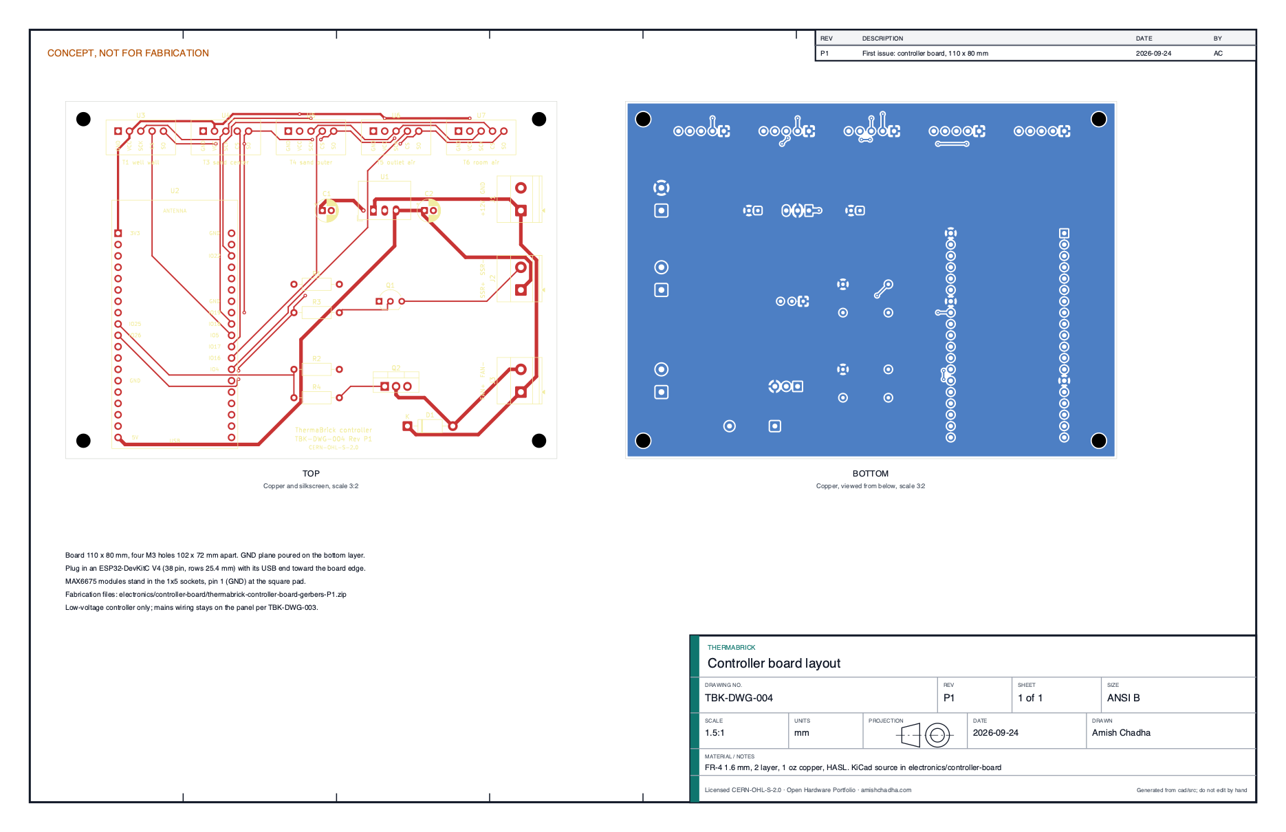
cad/drawings/TBK-DWG-004.png
