BoujeeEnjinia1701/thermabrick/cad/drawings/TBK-DWG-005.png

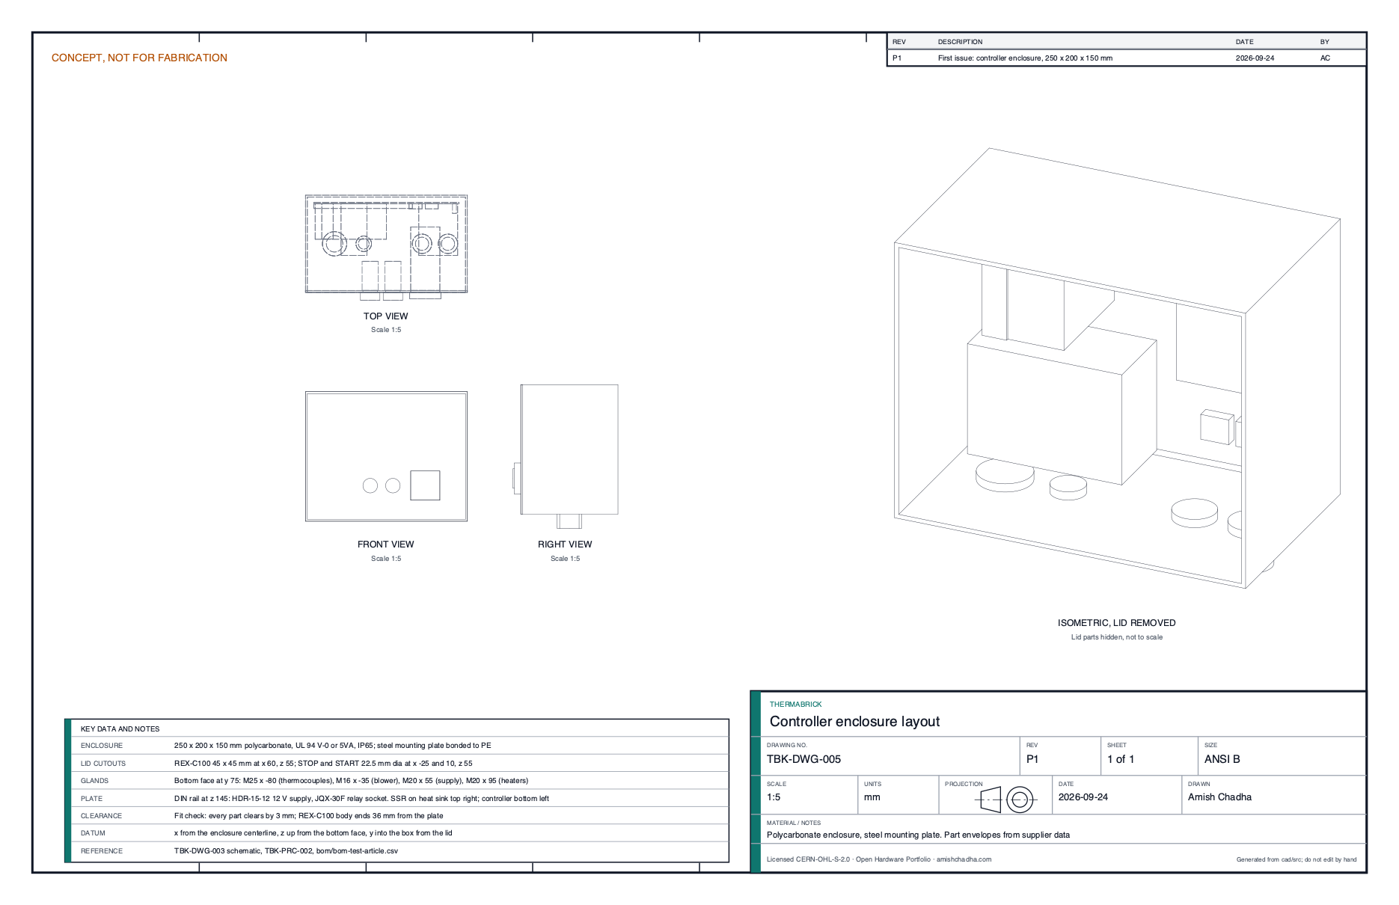
cad/drawings/TBK-DWG-005.png
