BoujeeEnjinia1701/thermabrick/media/card.png

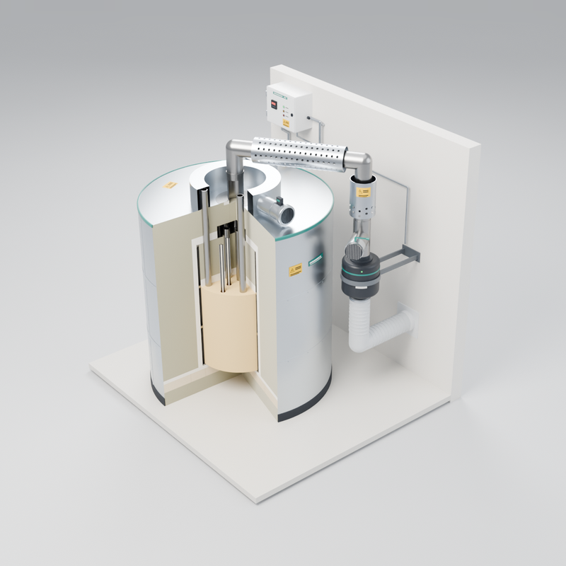
media/card.png
