BoujeeEnjinia1701/thermabrick/media/concept-blueprint.png

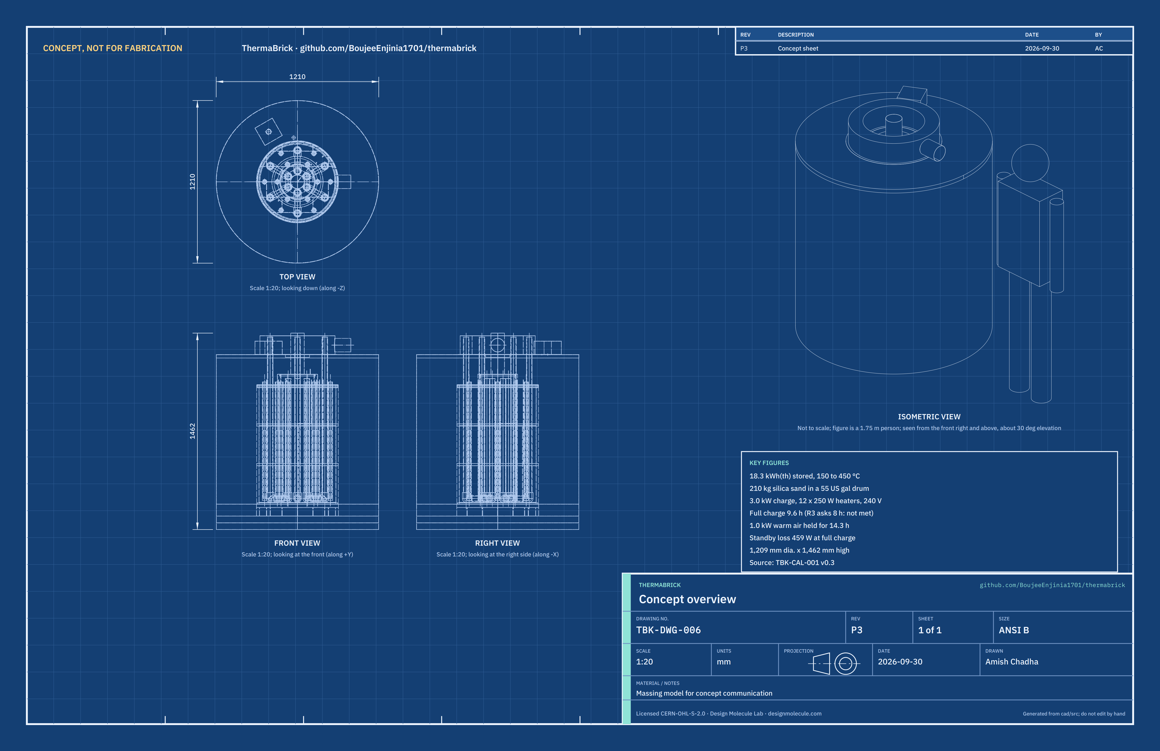
media/concept-blueprint.png
