BoujeeEnjinia1701/thermabrick/media/cutaway.png

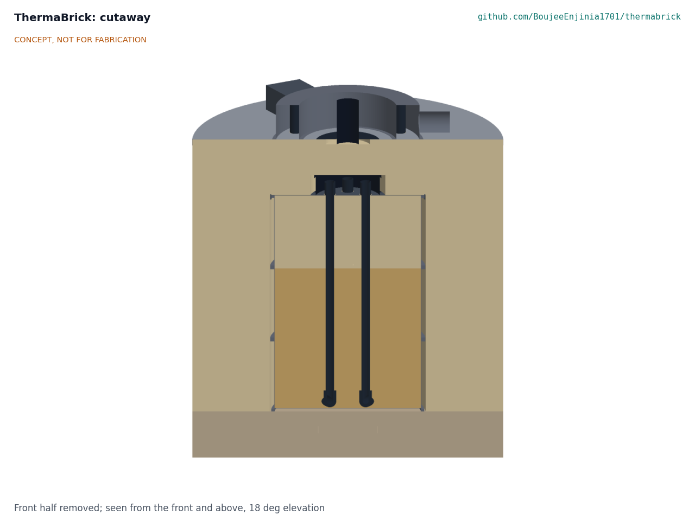
media/cutaway.png
