BoujeeEnjinia1701/thermabrick/media/exploded.png

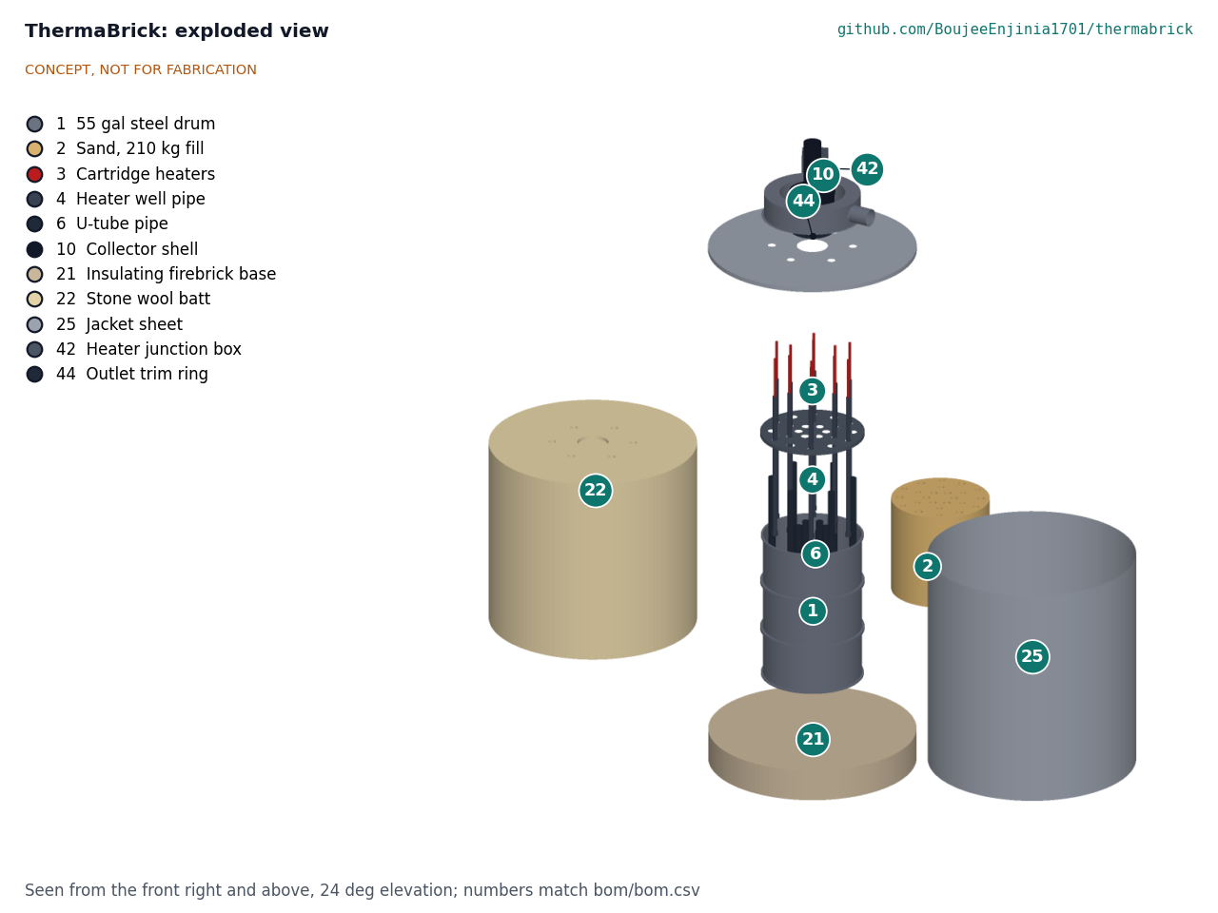
media/exploded.png
