BoujeeEnjinia1701/thermabrick/media/flow.png

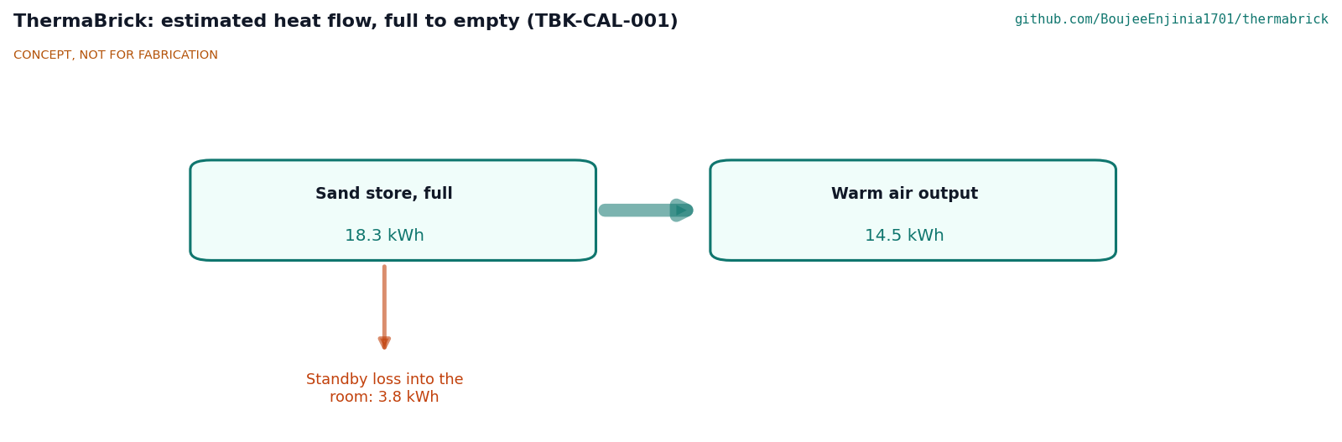
media/flow.png
