BoujeeEnjinia1701/thermabrick/media/hero.png

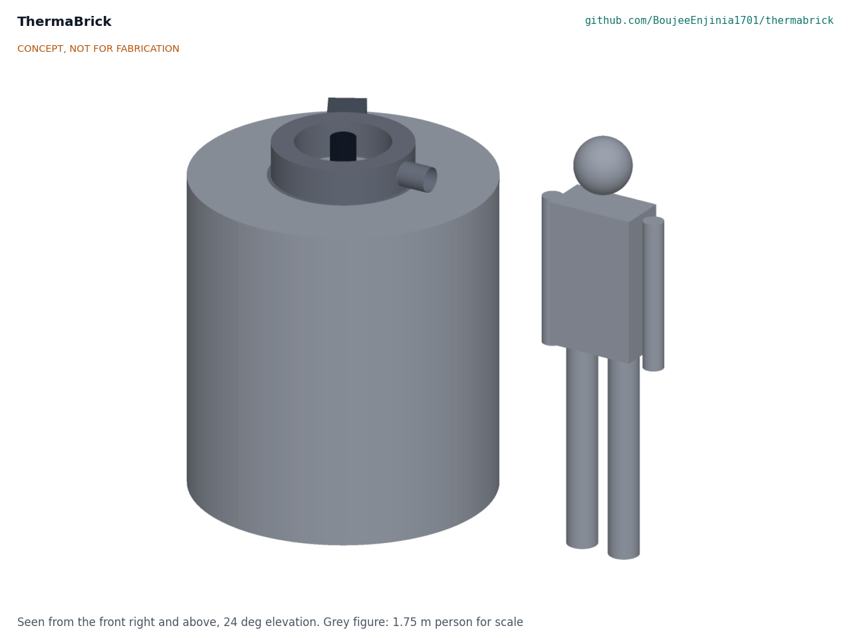
media/hero.png
