BoujeeEnjinia1701/thermabrick/media/render-detail.png

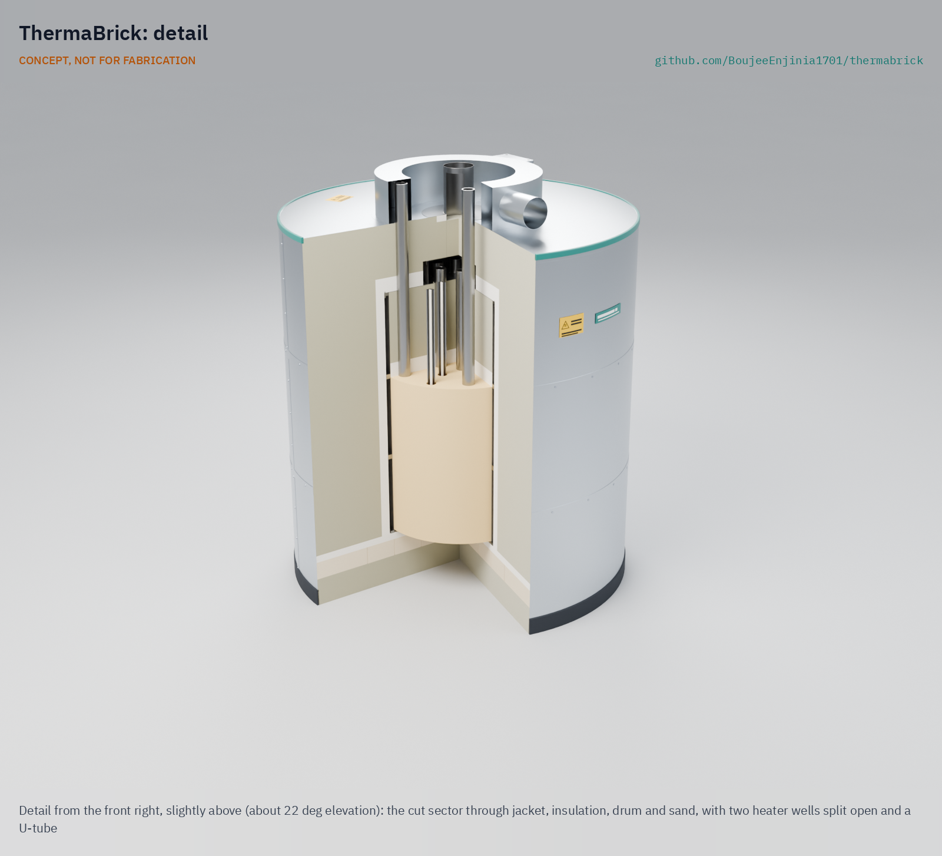
media/render-detail.png
