BoujeeEnjinia1701/thermabrick/media/render-exploded.png

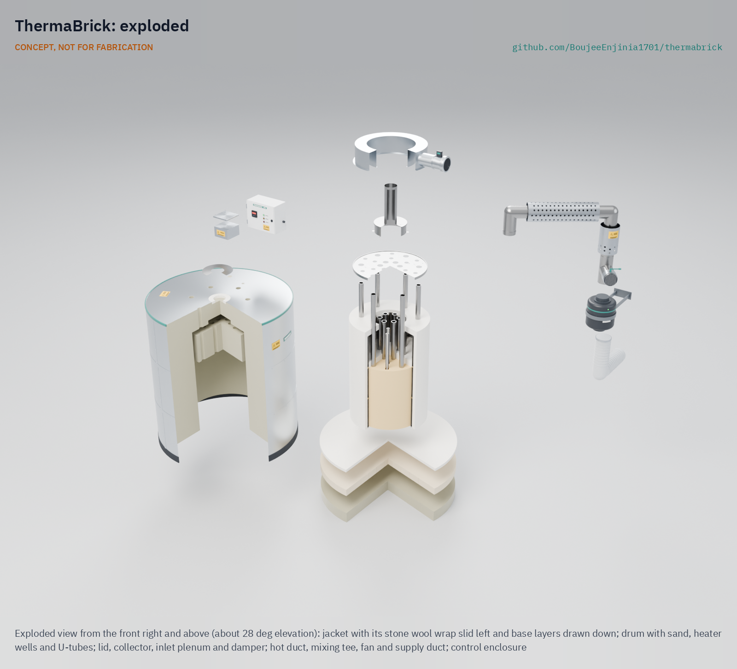
media/render-exploded.png
