BoujeeEnjinia1701/thermabrick/media/social-preview.png

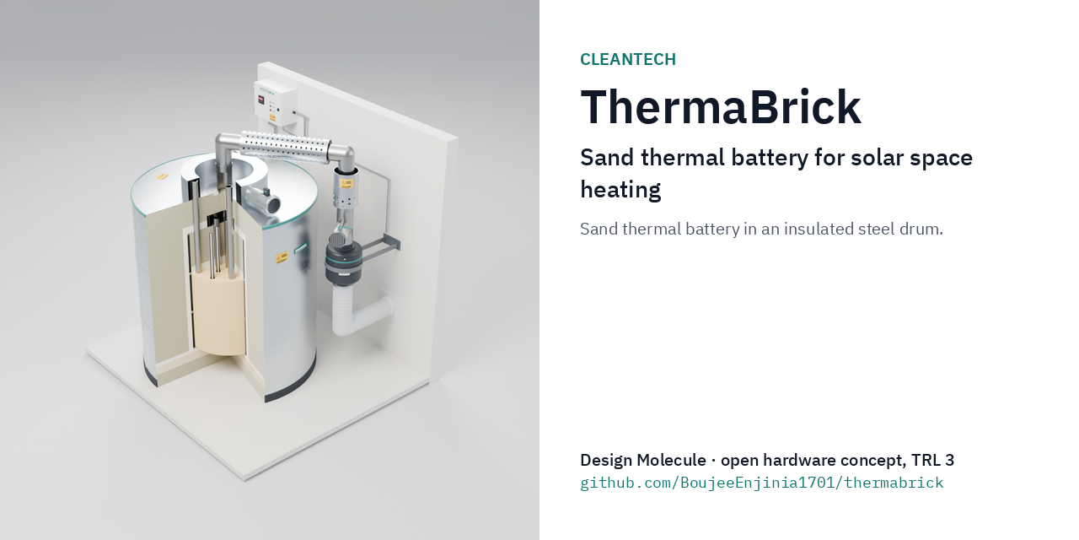
media/social-preview.png
