BoujeeEnjinia1701/thermabrick/docs/05-build-plan/joint-04.png

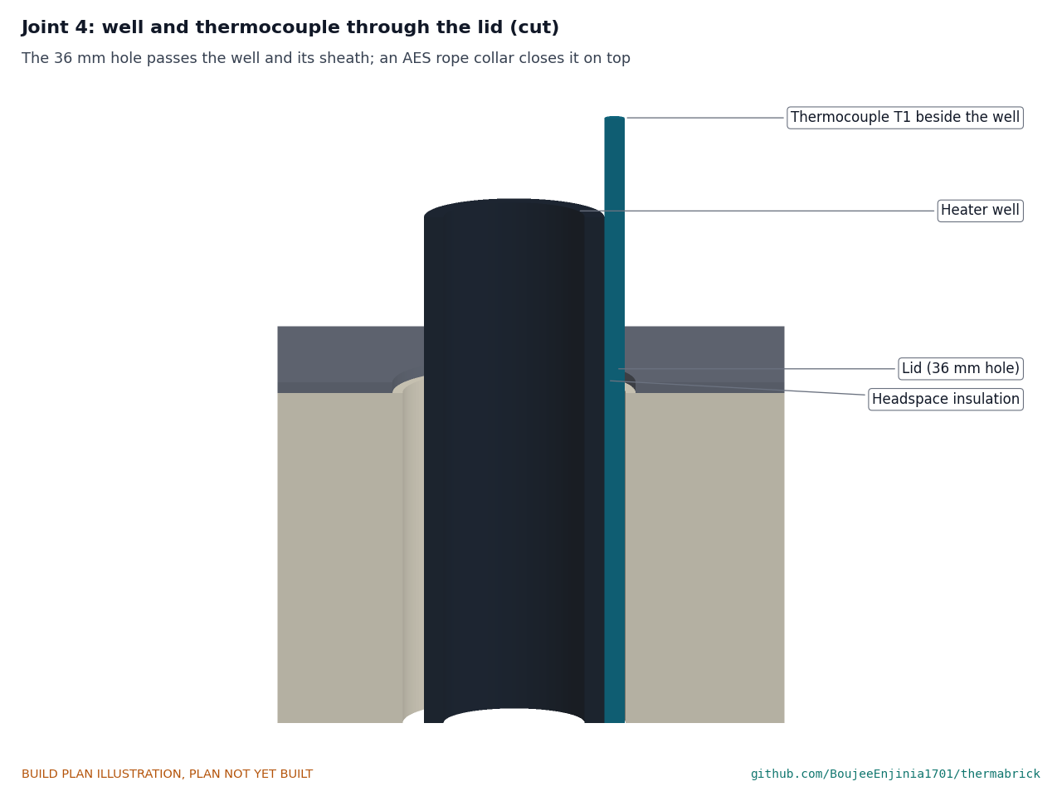
docs/05-build-plan/joint-04.png
