BoujeeEnjinia1701/thermabrick/archive/out-of-phase-trl4/docs/05-tests/results/selftest/synthetic_TP3.csv

# synthetic record from tbk_tst_001_fit.py selftest
host_time | seq | t_s | T1_C | T3_C | T4_C | T5_C | T6_C | heater_mode | setpoint_C | heater_duty | heater_W | heater_Wh | blower_mode | blower_duty | airflow_Ls | exchanger_W | faults
2026-01-01T08:00:00+00:00 | 1 | 0 | 180.69 | 148.62 | 152.29 |  | 20.00 | 1 | 550.0 | 1.020 | 1019.9 | 0 | 0 | 0.000 | 0.00 |  | 0
2026-01-01T08:00:10+00:00 | 2 | 10 | 197.70 | 148.88 | 151.50 |  | 20.00 | 1 | 550.0 | 1.020 | 1019.9 | 0 | 0 | 0.000 | 0.00 |  | 0
2026-01-01T08:00:20+00:00 | 3 | 20 | 213.25 | 149.80 | 148.10 |  | 20.00 | 1 | 550.0 | 1.020 | 1019.9 | 0 | 0 | 0.000 | 0.00 |  | 0
2026-01-01T08:00:30+00:00 | 4 | 30 | 227.09 | 148.38 | 147.21 |  | 20.00 | 1 | 550.0 | 1.020 | 1019.9 | 0 | 0 | 0.000 | 0.00 |  | 0
2026-01-01T08:00:40+00:00 | 5 | 40 | 237.83 | 152.52 | 149.95 |  | 20.00 | 1 | 550.0 | 1.020 | 1019.9 | 0 | 0 | 0.000 | 0.00 |  | 0
2026-01-01T08:00:50+00:00 | 6 | 50 | 244.58 | 149.89 | 149.55 |  | 20.00 | 1 | 550.0 | 1.020 | 1019.9 | 0 | 0 | 0.000 | 0.00 |  | 0
2026-01-01T08:01:00+00:00 | 7 | 60 | 250.53 | 151.21 | 151.02 |  | 20.00 | 1 | 550.0 | 1.020 | 1019.9 | 0 | 0 | 0.000 | 0.00 |  | 0
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
