BoujeeEnjinia1701/thermabrick/archive/out-of-phase-trl4/docs/05-tests/results/selftest/synthetic_TP4.csv

# synthetic record from tbk_tst_001_fit.py selftest
host_time | seq | t_s | T1_C | T3_C | T4_C | T5_C | T6_C | heater_mode | setpoint_C | heater_duty | heater_W | heater_Wh | blower_mode | blower_duty | airflow_Ls | exchanger_W | faults
2026-01-01T23:00:00+00:00 | 1 | 0 | 541.37 | 389.64 | 460.64 |  | 20.00 | 1 | 550.0 | 0.000 | 0.0 | 0 | 0 | 0.000 | 0.00 |  | 0
2026-01-01T23:00:10+00:00 | 2 | 10 | 534.63 | 390.64 | 459.64 |  | 20.00 | 1 | 550.0 | 0.000 | 0.0 | 0 | 0 | 0.000 | 0.00 |  | 0
2026-01-01T23:00:20+00:00 | 3 | 20 | 531.33 | 386.55 | 459.69 |  | 20.00 | 1 | 550.0 | 0.000 | 0.0 | 0 | 0 | 0.000 | 0.00 |  | 0
2026-01-01T23:00:30+00:00 | 4 | 30 | 527.12 | 388.61 | 461.56 |  | 20.00 | 1 | 550.0 | 0.000 | 0.0 | 0 | 0 | 0.000 | 0.00 |  | 0
2026-01-01T23:00:40+00:00 | 5 | 40 | 524.91 | 386.85 | 460.93 |  | 20.00 | 1 | 550.0 | 0.000 | 0.0 | 0 | 0 | 0.000 | 0.00 |  | 0
2026-01-01T23:00:50+00:00 | 6 | 50 | 521.24 | 391.01 | 460.48 |  | 20.00 | 1 | 550.0 | 0.000 | 0.0 | 0 | 0 | 0.000 | 0.00 |  | 0
2026-01-01T23:01:00+00:00 | 7 | 60 | 521.27 | 386.29 | 458.96 |  | 20.00 | 1 | 550.0 | 0.000 | 0.0 | 0 | 0 | 0.000 | 0.00 |  | 0
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
