BoujeeEnjinia1701/thermabrick/archive/out-of-phase-trl4/docs/05-tests/results/selftest/synthetic_TP5.csv

host_time | seq | t_s | T1_C | T3_C | T4_C | T5_C | T6_C | heater_mode | setpoint_C | heater_duty | heater_W | heater_Wh | blower_mode | blower_duty | airflow_Ls | exchanger_W | faults
2026-01-01T08:00:00+00:00 | 1 | 0 |  | 420.00 | 420.00 |  | 20.00 | 0 | 550.0 | 0 | 0 | 0 | 1 | 0.5 | 1.00 | 200.2 | 0
2026-01-01T08:00:10+00:00 | 2 | 10 |  | 420.00 | 420.00 |  | 20.00 | 0 | 550.0 | 0 | 0 | 0 | 1 | 0.5 | 1.00 | 192.7 | 0
2026-01-01T08:00:20+00:00 | 3 | 20 |  | 420.00 | 420.00 |  | 20.00 | 0 | 550.0 | 0 | 0 | 0 | 1 | 0.5 | 1.00 | 201.4 | 0
2026-01-01T08:00:30+00:00 | 4 | 30 |  | 420.00 | 420.00 |  | 20.00 | 0 | 550.0 | 0 | 0 | 0 | 1 | 0.5 | 1.00 | 208.9 | 0
2026-01-01T08:00:40+00:00 | 5 | 40 |  | 420.00 | 420.00 |  | 20.00 | 0 | 550.0 | 0 | 0 | 0 | 1 | 0.5 | 1.00 | 196.0 | 0
2026-01-01T08:00:50+00:00 | 6 | 50 |  | 420.00 | 420.00 |  | 20.00 | 0 | 550.0 | 0 | 0 | 0 | 1 | 0.5 | 1.00 | 198.4 | 0
2026-01-01T08:01:00+00:00 | 7 | 60 |  | 420.00 | 420.00 |  | 20.00 | 0 | 550.0 | 0 | 0 | 0 | 1 | 0.5 | 1.00 | 186.7 | 0
2026-01-01T08:01:10+00:00 | 8 | 70 |  | 420.00 | 420.00 |  | 20.00 | 0 | 550.0 | 0 | 0 | 0 | 1 | 0.5 | 1.00 | 184.5 | 0
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
