BoujeeEnjinia1701/thermabrick/cad/drawings/TBK-DWG-003.pdf

## CONCEPT, NOT FOR FABRICATION

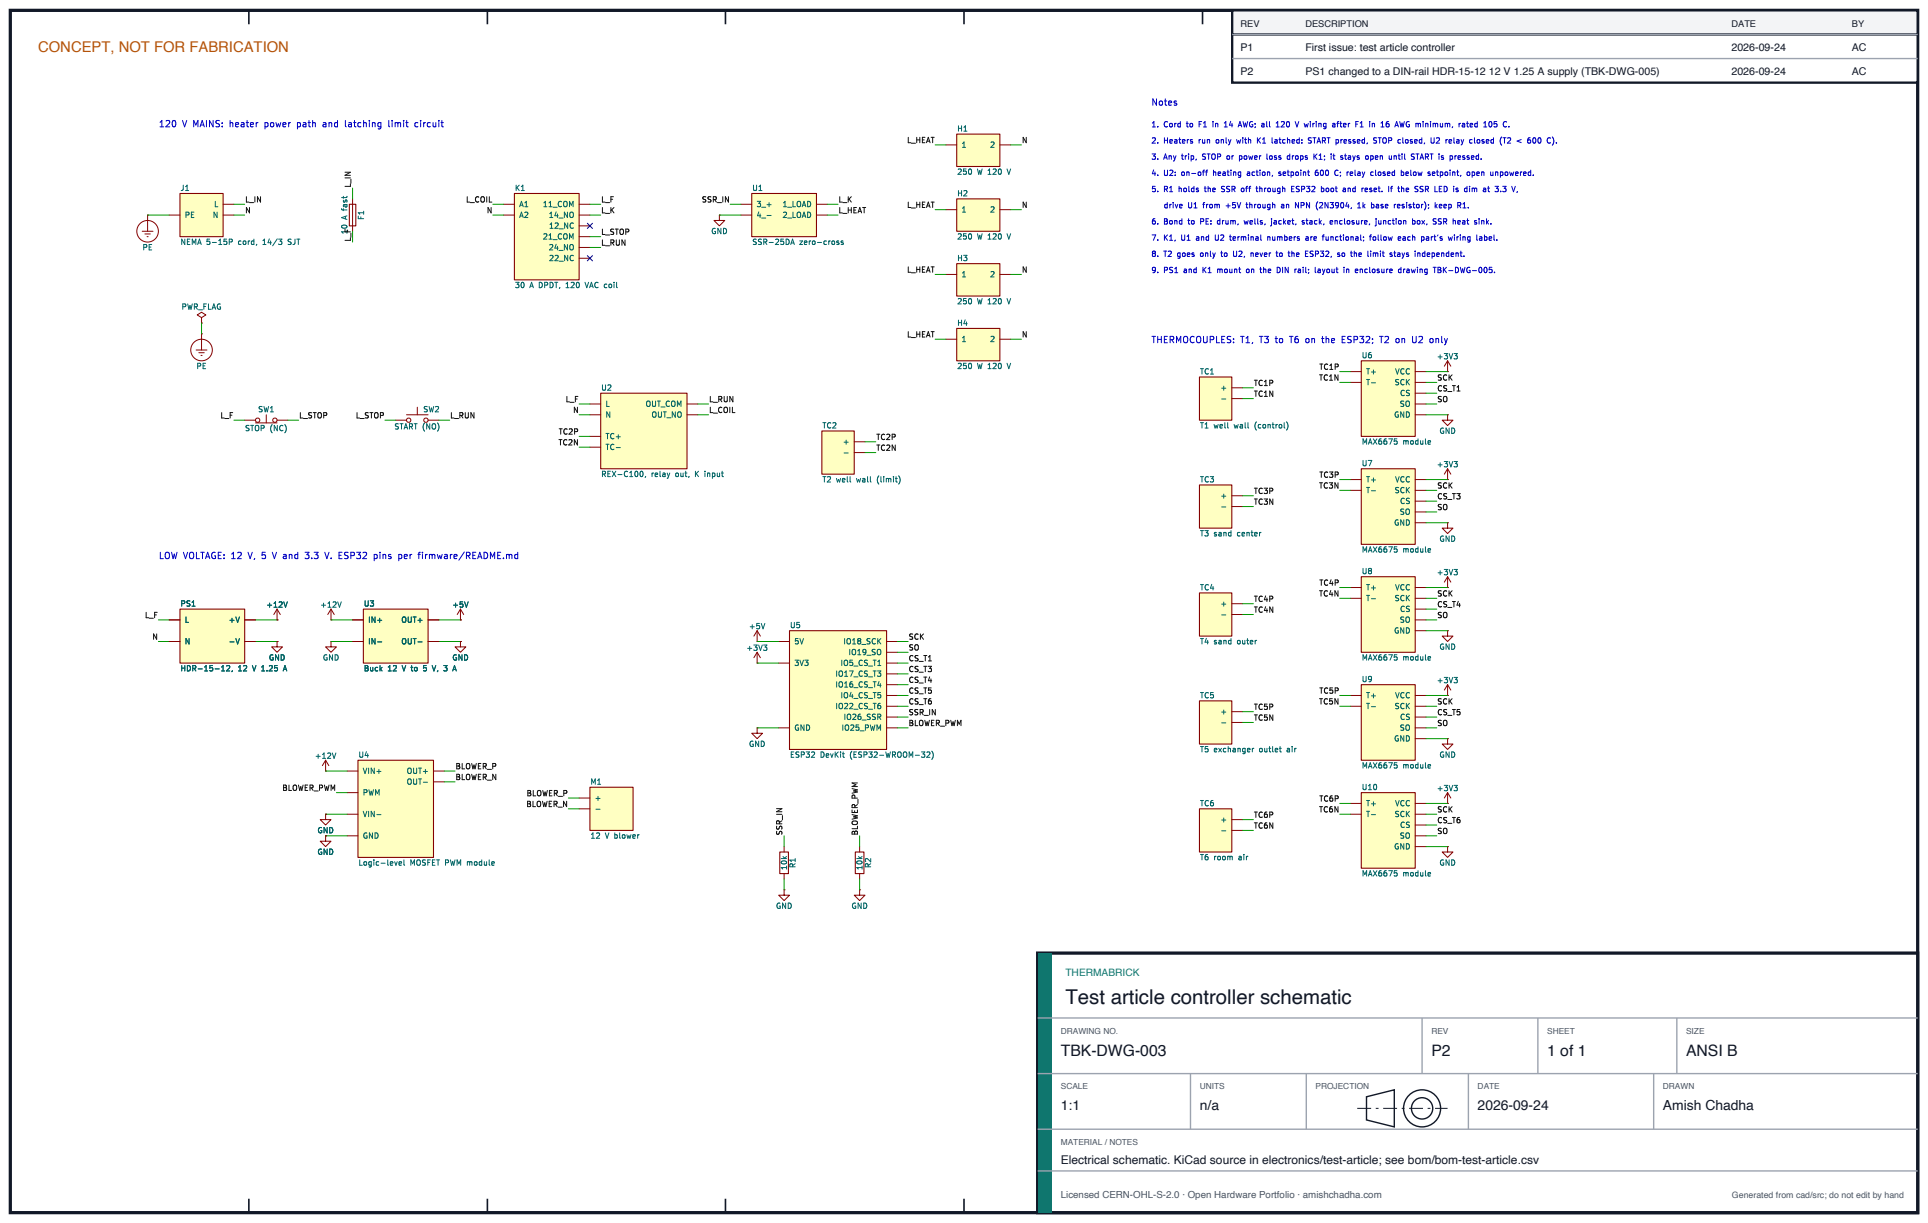
[picture p81: page 1]
REV; DESCRIPTION; DATE; First issue: test article controller; PS1 changed to a DIN-rail HDR-15-12 12 V 1.25 A supply (TBK-DWG-005); DRAWING NO. TBK-DWG-003; REV P2; SHEET 1 of 1; SIZE ANSI B; SCALE 1:1; UNITS n/a; PROJECTION; DRAWN Amish Chadha; Licensed CERN-OHL-S-2.0 · Open Hardware Portfolio · amishchadha.com; Generated from cad/src; do not edit by hand

THERMABRICK
Test article controller schematic

MATERIAL / NOTES
Electrical schematic. KiCad source in electronics/test-article; see bom/bom-test-article.csv
