BoujeeEnjinia1701/thermabrick/cad/drawings/TBK-DWG-004.pdf

### CONCEPT, NOT FOR FABRICATION

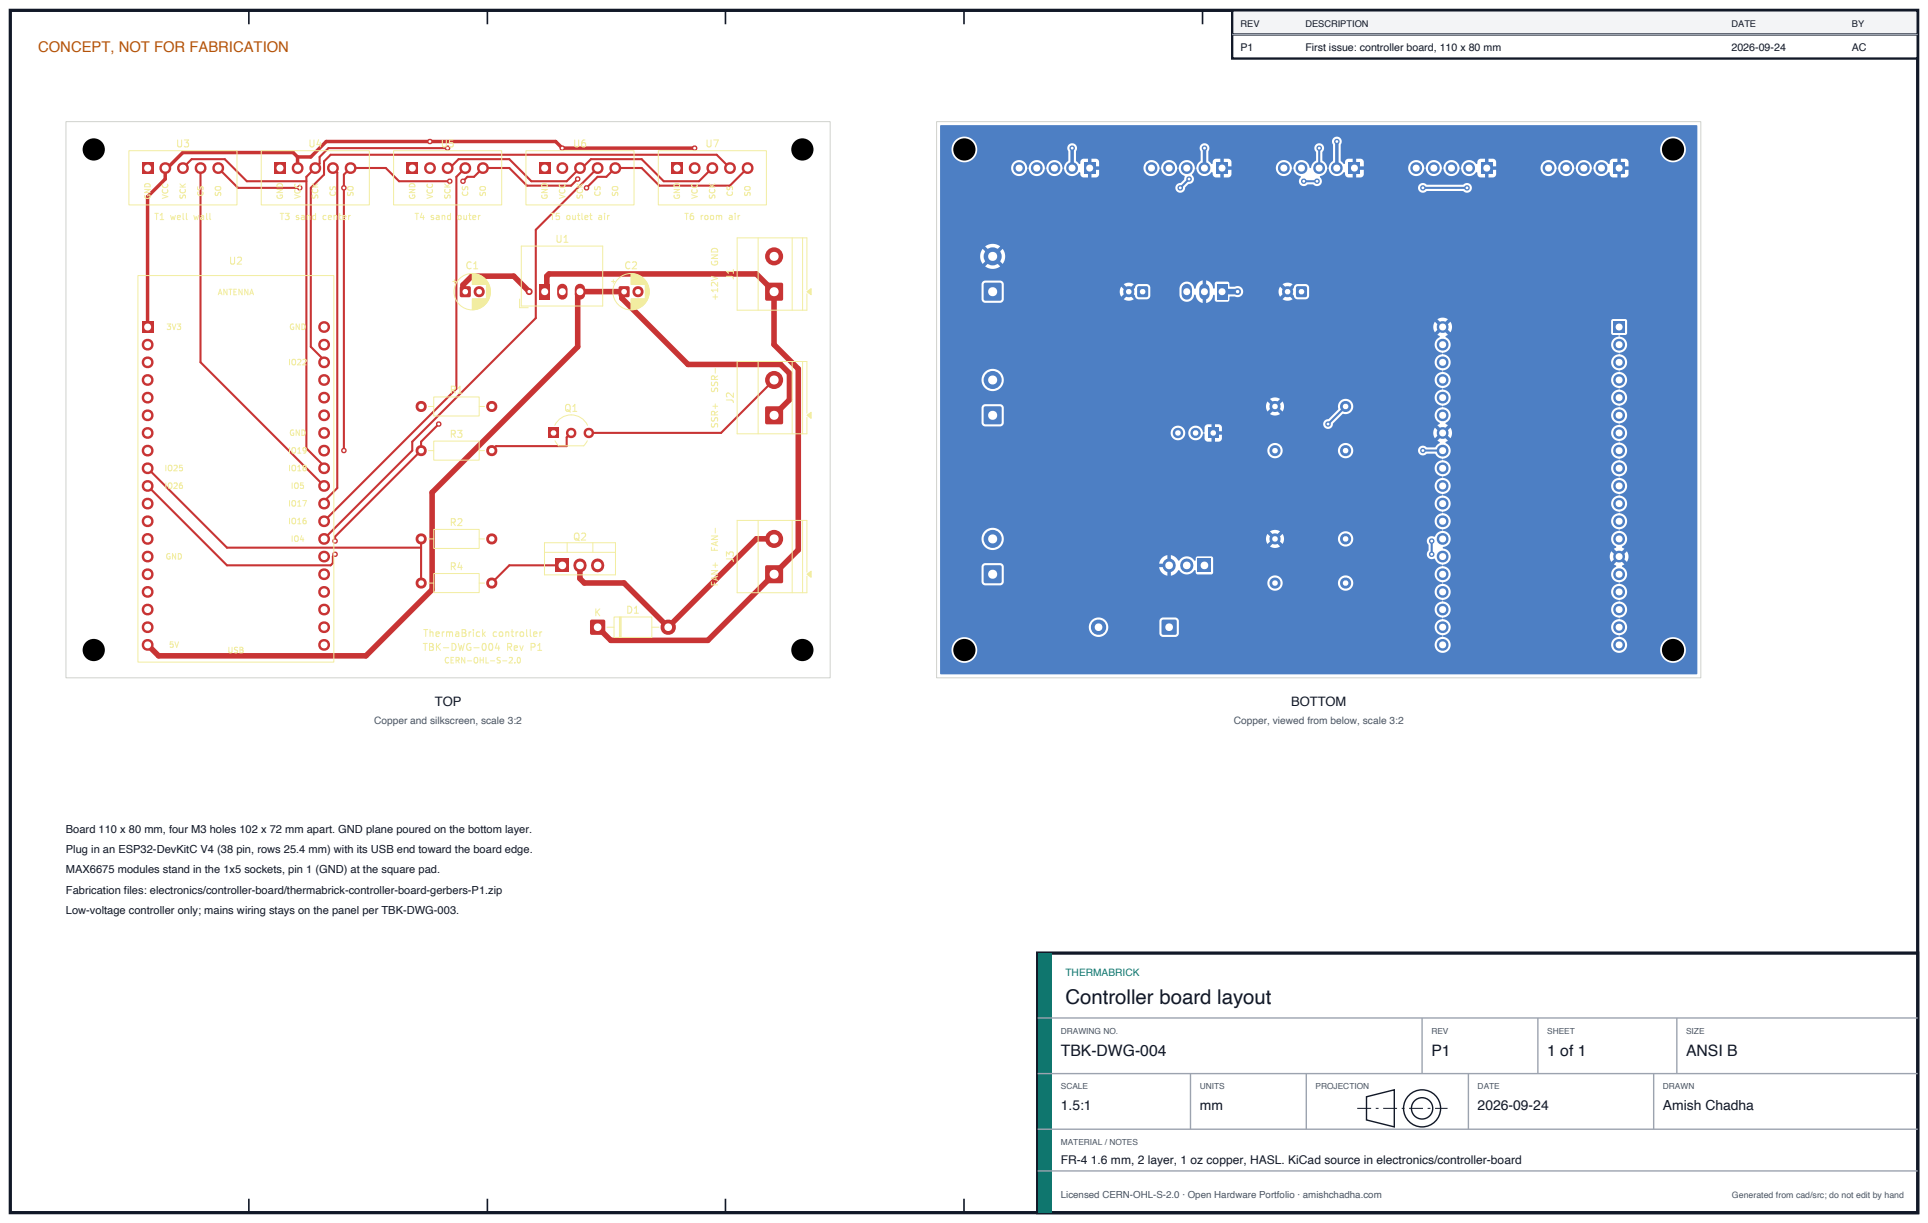
[picture p82: page 1]
TOP; BOTTOM; REV; DESCRIPTION; DATE; First issue: controller board, 110 x 80 mm; DRAWING NO. TBK-DWG-004; REV P1; SHEET 1 of 1; SIZE ANSI B; SCALE 1.5:1; UNITS mm; PROJECTION; DRAWN Amish Chadha; Licensed CERN-OHL-S-2.0 · Open Hardware Portfolio · amishchadha.com; Generated from cad/src; do not edit by hand

Copper and silkscreen, scale 3:2

Copper, viewed from below, scale 3:2

Board 110 x 80 mm, four M3 holes 102 x 72 mm apart. GND plane poured on the bottom layer.
Plug in an ESP32-DevKitC V4 (38 pin, rows 25.4 mm) with its USB end toward the board edge.
MAX6675 modules stand in the 1x5 sockets, pin 1 (GND) at the square pad.
Fabrication files: electronics/controller-board/thermabrick-controller-board-gerbers-P1.zip
Low-voltage controller only; mains wiring stays on the panel per TBK-DWG-003.

THERMABRICK
Controller board layout

MATERIAL / NOTES
FR-4 1.6 mm, 2 layer, 1 oz copper, HASL. KiCad source in electronics/controller-board
