BoujeeEnjinia1701/thermabrick/electronics/test-article/thermabrick-test-article.pdf

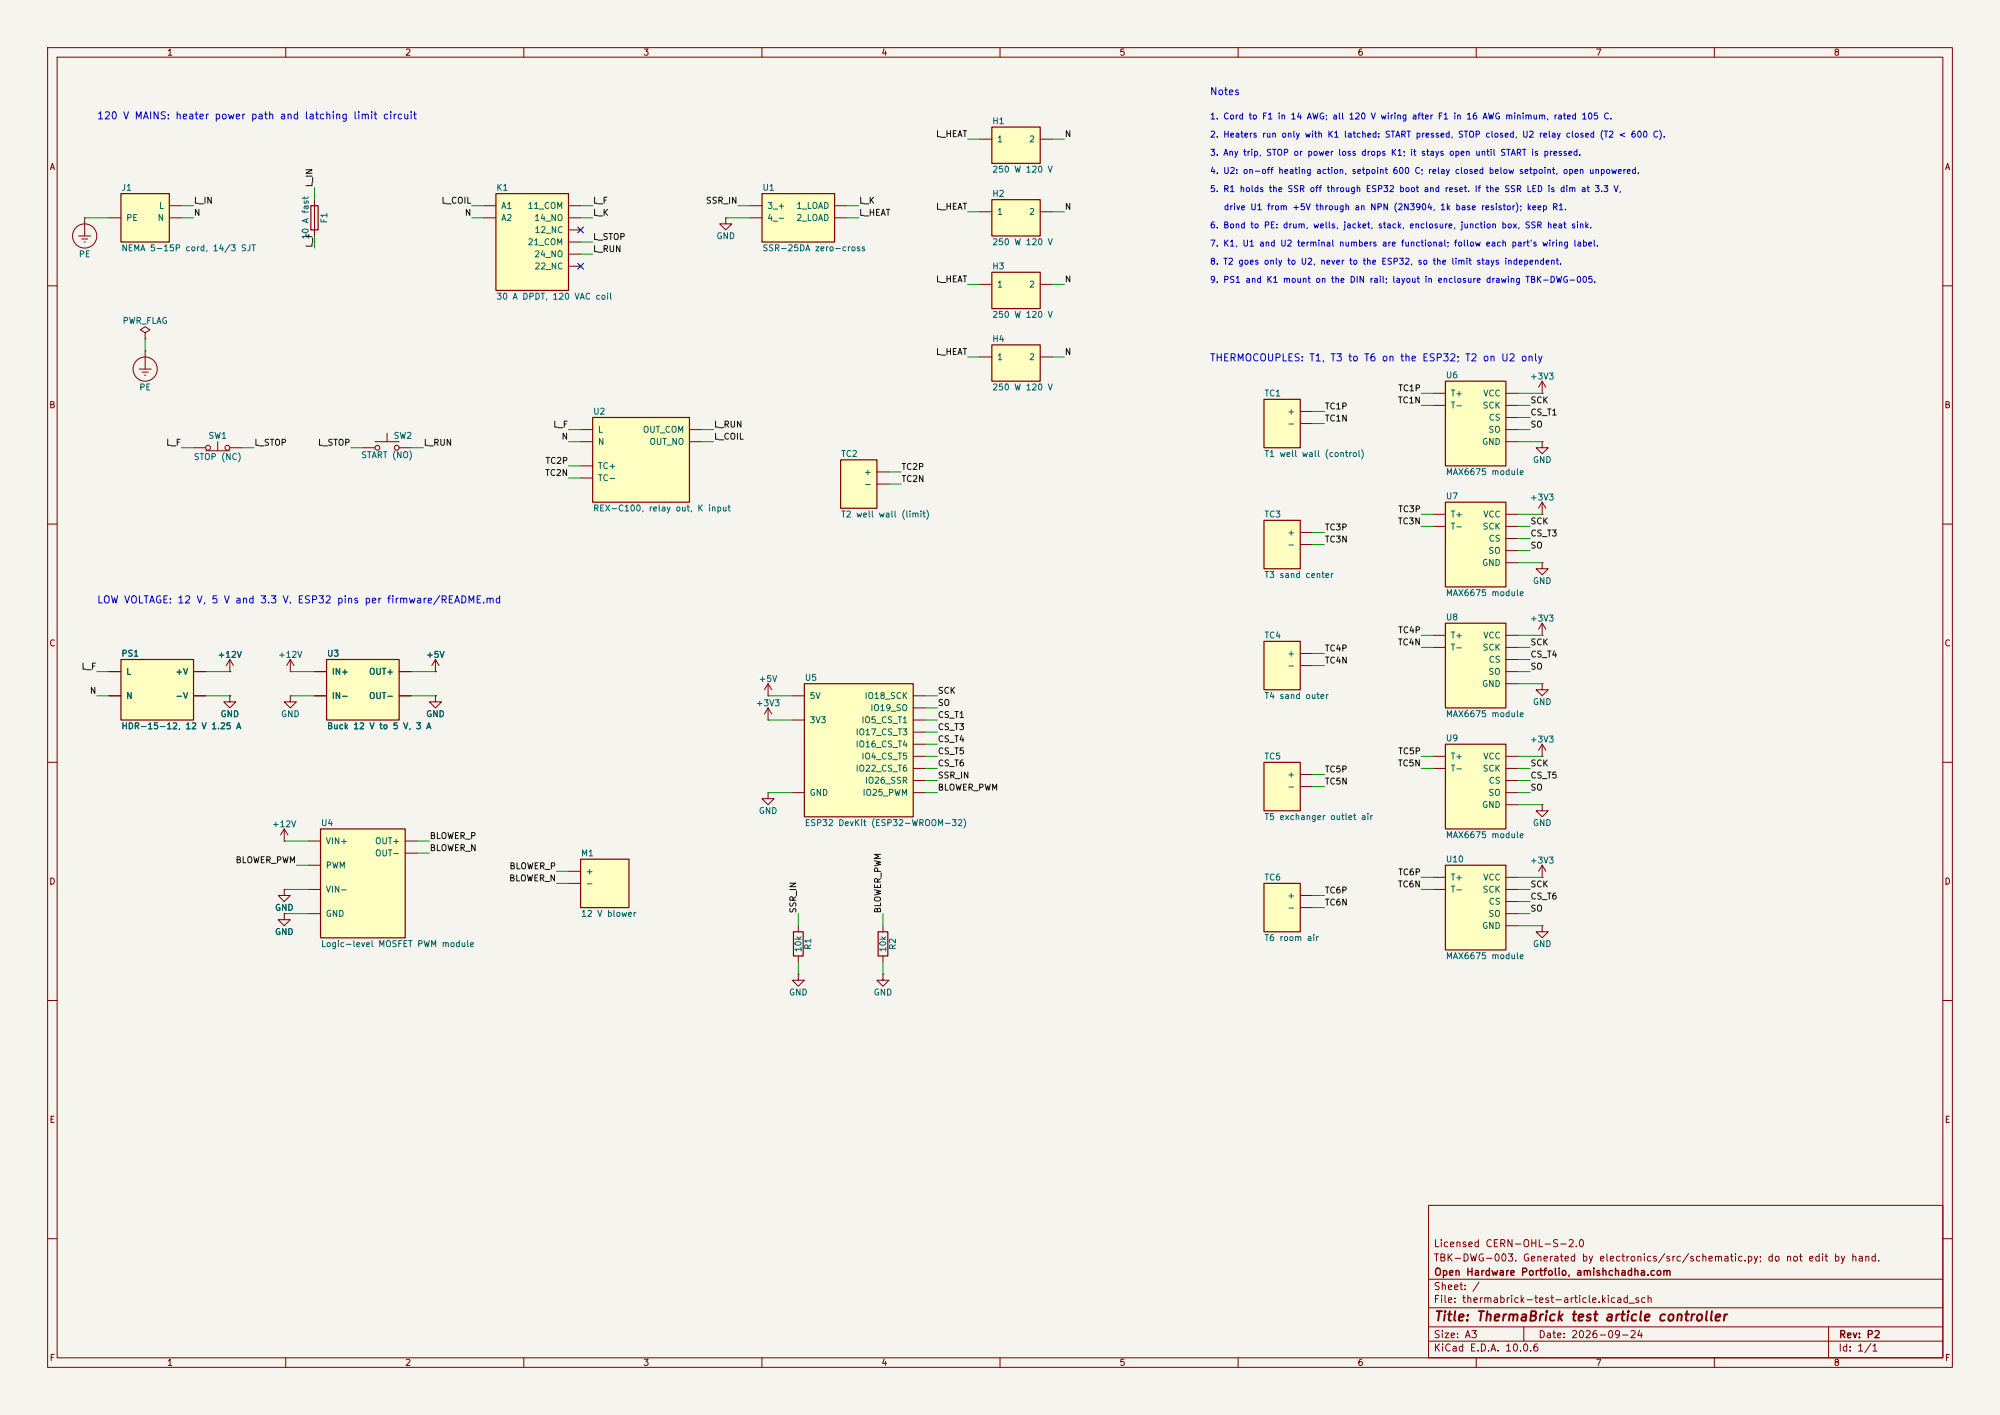
[picture p83: page 1]

LOW VOLTAGE: 12 V, 5 V and 3.3 V. ESP32 pins per firmware/README.md
GND +12V

Licensed CERN-OHL-S-2.0
TBK-DWG-003. Generated by electronics/src/schematic.py; do not edit by hand.
Open Hardware Portfolio, amishchadha.com
Sheet: /
File: thermabrick-test-article.kicad_sch
Title: ThermaBrick test article controller

Size: A3 | Rev: P2 | F Date: 2026-09-24
KiCad E.D.A. 10.0.6 | Id: 1/1
