BoujeeEnjinia1701/thermabrick/firmware/include/secrets.example.h

// Copy to secrets.h (git-ignored) and fill in. Licensed MIT (see LICENSE-SOFTWARE).
#pragma once
#define WIFI_SSID "your-network"
#define WIFI_PASS "your-password"
// Every HTTP request must carry ?token=... when this is non-empty. Strongly recommended.
#define API_TOKEN "change-me"
